trailcurrentoss/TrailCurrentWaveshareEsp32s3Remote/src/ui/screens.c

#include <string.h>

#include "screens.h"
#include "images.h"
#include "fonts.h"
#include "actions.h"
#include "vars.h"
#include "styles.h"
#include "ui.h"

#include <string.h>

objects_t objects;
lv_obj_t *tick_value_change_obj;
uint32_t active_theme_index = 0;

void create_screen_home() {
    lv_obj_t *obj = lv_obj_create(0);
    objects.home = obj;
    lv_obj_set_pos(obj, 0, 0);
    lv_obj_set_size(obj, 800, 480);
    add_style_style_screen_default(obj);
    {
        lv_obj_t *parent_obj = obj;
        {
            // HomePageBottomNavBar
            lv_obj_t *obj = lv_obj_create(parent_obj);
            objects.home_page_bottom_nav_bar = obj;
            lv_obj_set_pos(obj, 0, 0);
            lv_obj_set_size(obj, 800, 60);
            lv_obj_set_style_pad_left(obj, 0, LV_PART_MAIN | LV_STATE_DEFAULT);
            lv_obj_set_style_pad_top(obj, 0, LV_PART_MAIN | LV_STATE_DEFAULT);
            lv_obj_set_style_pad_right(obj, 0, LV_PART_MAIN | LV_STATE_DEFAULT);
            lv_obj_set_style_pad_bottom(obj, 0, LV_PART_MAIN | LV_STATE_DEFAULT);
            lv_obj_set_style_bg_opa(obj, 0, LV_PART_MAIN | LV_STATE_DEFAULT);
            lv_obj_set_style_border_width(obj, 0, LV_PART_MAIN | LV_STATE_DEFAULT);
            create_user_widget_bottom_nav_bar(obj, 10);
            lv_obj_set_style_align(obj, LV_ALIGN_BOTTOM_LEFT, LV_PART_MAIN | LV_STATE_DEFAULT);
        }
        {
            lv_obj_t *obj = lv_obj_create(parent_obj);
            lv_obj_set_pos(obj, -310, 30);
            lv_obj_set_size(obj, 150, 150);
            lv_obj_clear_flag(obj, LV_OBJ_FLAG_CLICKABLE|LV_OBJ_FLAG_CLICK_FOCUSABLE|LV_OBJ_FLAG_GESTURE_BUBBLE|LV_OBJ_FLAG_PRESS_LOCK|LV_OBJ_FLAG_SCROLLABLE|LV_OBJ_FLAG_SCROLL_CHAIN_HOR|LV_OBJ_FLAG_SCROLL_CHAIN_VER|LV_OBJ_FLAG_SCROLL_ELASTIC|LV_OBJ_FLAG_SCROLL_MOMENTUM|LV_OBJ_FLAG_SCROLL_WITH_ARROW|LV_OBJ_FLAG_SNAPPABLE);
            add_style_panel_nav_bar(obj);
            lv_obj_set_style_align(obj, LV_ALIGN_TOP_MID, LV_PART_MAIN | LV_STATE_DEFAULT);
            {
                lv_obj_t *parent_obj = obj;
                {
                    // LabelWarningIconTrailerConnected
                    lv_obj_t *obj = lv_label_create(parent_obj);
                    objects.label_warning_icon_trailer_connected = obj;
                    lv_obj_set_pos(obj, 0, 20);
                    lv_obj_set_size(obj, LV_SIZE_CONTENT, LV_SIZE_CONTENT);
                    add_style_label_fa32_icon(obj);
                    lv_obj_set_style_text_color(obj, lv_color_hex(theme_colors[active_theme_index][0]), LV_PART_MAIN | LV_STATE_DEFAULT);
                    lv_obj_set_style_align(obj, LV_ALIGN_TOP_MID, LV_PART_MAIN | LV_STATE_DEFAULT);
                    lv_obj_set_style_text_color(obj, lv_color_hex(theme_colors[active_theme_index][8]), LV_PART_MAIN | LV_STATE_CHECKED);
                    lv_label_set_text(obj, "\uf8ff");
                }
                {
                    // LabelWarningTextTrailerConnected
                    lv_obj_t *obj = lv_label_create(parent_obj);
                    objects.label_warning_text_trailer_connected = obj;
                    lv_obj_set_pos(obj, 0, 0);
                    lv_obj_set_size(obj, LV_SIZE_CONTENT, LV_SIZE_CONTENT);
                    add_style_label_default(obj);
                    lv_obj_set_style_text_color(obj, lv_color_hex(theme_colors[active_theme_index][0]), LV_PART_MAIN | LV_STATE_DEFAULT);
                    lv_obj_set_style_align(obj, LV_ALIGN_BOTTOM_MID, LV_PART_MAIN | LV_STATE_DEFAULT);
                    lv_obj_set_style_text_align(obj, LV_TEXT_ALIGN_CENTER, LV_PART_MAIN | LV_STATE_DEFAULT);
                    lv_obj_set_style_text_font(obj, &lv_font_montserrat_24, LV_PART_MAIN | LV_STATE_DEFAULT);
                    lv_obj_set_style_text_color(obj, lv_color_hex(theme_colors[active_theme_index][8]), LV_PART_MAIN | LV_STATE_CHECKED);
                    lv_obj_set_style_align(obj, LV_ALIGN_BOTTOM_MID, LV_PART_MAIN | LV_STATE_CHECKED);
                    lv_obj_set_style_text_font(obj, &lv_font_montserrat_24, LV_PART_MAIN | LV_STATE_CHECKED);
                    lv_label_set_text(obj, "Connected");
                }
            }
        }
        {
            lv_obj_t *obj = lv_obj_create(parent_obj);
            lv_obj_set_pos(obj, -155, 30);
            lv_obj_set_size(obj, 150, 150);
            lv_obj_clear_flag(obj, LV_OBJ_FLAG_CLICKABLE|LV_OBJ_FLAG_CLICK_FOCUSABLE|LV_OBJ_FLAG_GESTURE_BUBBLE|LV_OBJ_FLAG_PRESS_LOCK|LV_OBJ_FLAG_SCROLLABLE|LV_OBJ_FLAG_SCROLL_CHAIN_HOR|LV_OBJ_FLAG_SCROLL_CHAIN_VER|LV_OBJ_FLAG_SCROLL_ELASTIC|LV_OBJ_FLAG_SCROLL_MOMENTUM|LV_OBJ_FLAG_SCROLL_WITH_ARROW|LV_OBJ_FLAG_SNAPPABLE);
            add_style_panel_nav_bar(obj);
            lv_obj_set_style_align(obj, LV_ALIGN_TOP_MID, LV_PART_MAIN | LV_STATE_DEFAULT);
            {
                lv_obj_t *parent_obj = obj;
                {
                    // LabelWarningIconFridge
                    lv_obj_t *obj = lv_label_create(parent_obj);
                    objects.label_warning_icon_fridge = obj;
                    lv_obj_set_pos(obj, 0, 20);
                    lv_obj_set_size(obj, LV_SIZE_CONTENT, LV_SIZE_CONTENT);
                    add_style_label_fa32_icon(obj);
                    lv_obj_set_style_text_color(obj, lv_color_hex(theme_colors[active_theme_index][0]), LV_PART_MAIN | LV_STATE_DEFAULT);
                    lv_obj_set_style_align(obj, LV_ALIGN_TOP_MID, LV_PART_MAIN | LV_STATE_DEFAULT);
                    lv_obj_set_style_text_color(obj, lv_color_hex(theme_colors[active_theme_index][8]), LV_PART_MAIN | LV_STATE_CHECKED);
                    lv_label_set_text(obj, "\uf2dc");
                }
                {
                    // LabelWarningTextFridge
                    lv_obj_t *obj = lv_label_create(parent_obj);
                    objects.label_warning_text_fridge = obj;
                    lv_obj_set_pos(obj, 0, 0);
                    lv_obj_set_size(obj, LV_SIZE_CONTENT, LV_SIZE_CONTENT);
                    add_style_label_default(obj);
                    lv_obj_set_style_text_color(obj, lv_color_hex(theme_colors[active_theme_index][0]), LV_PART_MAIN | LV_STATE_DEFAULT);
                    lv_obj_set_style_align(obj, LV_ALIGN_BOTTOM_MID, LV_PART_MAIN | LV_STATE_DEFAULT);
                    lv_obj_set_style_text_align(obj, LV_TEXT_ALIGN_CENTER, LV_PART_MAIN | LV_STATE_DEFAULT);
                    lv_obj_set_style_text_font(obj, &lv_font_montserrat_24, LV_PART_MAIN | LV_STATE_DEFAULT);
                    lv_obj_set_style_text_color(obj, lv_color_hex(theme_colors[active_theme_index][8]), LV_PART_MAIN | LV_STATE_CHECKED);
                    lv_obj_set_style_align(obj, LV_ALIGN_BOTTOM_MID, LV_PART_MAIN | LV_STATE_CHECKED);
                    lv_obj_set_style_text_font(obj, &lv_font_montserrat_24, LV_PART_MAIN | LV_STATE_CHECKED);
                    lv_label_set_text(obj, "Fridge");
                }
            }
        }
        {
            lv_obj_t *obj = lv_obj_create(parent_obj);
            lv_obj_set_pos(obj, 0, 30);
            lv_obj_set_size(obj, 150, 150);
            lv_obj_clear_flag(obj, LV_OBJ_FLAG_CLICKABLE|LV_OBJ_FLAG_CLICK_FOCUSABLE|LV_OBJ_FLAG_GESTURE_BUBBLE|LV_OBJ_FLAG_PRESS_LOCK|LV_OBJ_FLAG_SCROLLABLE|LV_OBJ_FLAG_SCROLL_CHAIN_HOR|LV_OBJ_FLAG_SCROLL_CHAIN_VER|LV_OBJ_FLAG_SCROLL_ELASTIC|LV_OBJ_FLAG_SCROLL_MOMENTUM|LV_OBJ_FLAG_SCROLL_WITH_ARROW|LV_OBJ_FLAG_SNAPPABLE);
            add_style_panel_nav_bar(obj);
            lv_obj_set_style_align(obj, LV_ALIGN_TOP_MID, LV_PART_MAIN | LV_STATE_DEFAULT);
            {
                lv_obj_t *parent_obj = obj;
                {
                    // LabelWarningIconRearDoor
                    lv_obj_t *obj = lv_label_create(parent_obj);
                    objects.label_warning_icon_rear_door = obj;
                    lv_obj_set_pos(obj, 0, 20);
                    lv_obj_set_size(obj, LV_SIZE_CONTENT, LV_SIZE_CONTENT);
                    add_style_label_fa32_icon(obj);
                    lv_obj_set_style_text_color(obj, lv_color_hex(theme_colors[active_theme_index][0]), LV_PART_MAIN | LV_STATE_DEFAULT);
                    lv_obj_set_style_align(obj, LV_ALIGN_TOP_MID, LV_PART_MAIN | LV_STATE_DEFAULT);
                    lv_obj_set_style_text_color(obj, lv_color_hex(theme_colors[active_theme_index][8]), LV_PART_MAIN | LV_STATE_CHECKED);
                    lv_label_set_text(obj, "\uf494");
                }
                {
                    // LabelWarningTextRearDoor
                    lv_obj_t *obj = lv_label_create(parent_obj);
                    objects.label_warning_text_rear_door = obj;
                    lv_obj_set_pos(obj, 0, 0);
                    lv_obj_set_size(obj, LV_SIZE_CONTENT, LV_SIZE_CONTENT);
                    add_style_label_default(obj);
                    lv_obj_set_style_text_color(obj, lv_color_hex(theme_colors[active_theme_index][0]), LV_PART_MAIN | LV_STATE_DEFAULT);
                    lv_obj_set_style_align(obj, LV_ALIGN_BOTTOM_MID, LV_PART_MAIN | LV_STATE_DEFAULT);
                    lv_obj_set_style_text_align(obj, LV_TEXT_ALIGN_CENTER, LV_PART_MAIN | LV_STATE_DEFAULT);
                    lv_obj_set_style_text_font(obj, &lv_font_montserrat_24, LV_PART_MAIN | LV_STATE_DEFAULT);
                    lv_obj_set_style_text_color(obj, lv_color_hex(theme_colors[active_theme_index][8]), LV_PART_MAIN | LV_STATE_CHECKED);
                    lv_obj_set_style_align(obj, LV_ALIGN_BOTTOM_MID, LV_PART_MAIN | LV_STATE_CHECKED);
                    lv_obj_set_style_text_font(obj, &lv_font_montserrat_24, LV_PART_MAIN | LV_STATE_CHECKED);
                    lv_label_set_text(obj, "Rear Door");
                }
            }
        }
        {
            lv_obj_t *obj = lv_obj_create(parent_obj);
            lv_obj_set_pos(obj, 155, 30);
            lv_obj_set_size(obj, 150, 150);
            lv_obj_clear_flag(obj, LV_OBJ_FLAG_CLICKABLE|LV_OBJ_FLAG_CLICK_FOCUSABLE|LV_OBJ_FLAG_GESTURE_BUBBLE|LV_OBJ_FLAG_PRESS_LOCK|LV_OBJ_FLAG_SCROLLABLE|LV_OBJ_FLAG_SCROLL_CHAIN_HOR|LV_OBJ_FLAG_SCROLL_CHAIN_VER|LV_OBJ_FLAG_SCROLL_ELASTIC|LV_OBJ_FLAG_SCROLL_MOMENTUM|LV_OBJ_FLAG_SCROLL_WITH_ARROW|LV_OBJ_FLAG_SNAPPABLE);
            add_style_panel_nav_bar(obj);
            lv_obj_set_style_align(obj, LV_ALIGN_TOP_MID, LV_PART_MAIN | LV_STATE_DEFAULT);
            {
                lv_obj_t *parent_obj = obj;
                {
                    // LabelWarningIconCabinets
                    lv_obj_t *obj = lv_label_create(parent_obj);
                    objects.label_warning_icon_cabinets = obj;
                    lv_obj_set_pos(obj, 0, 20);
                    lv_obj_set_size(obj, LV_SIZE_CONTENT, LV_SIZE_CONTENT);
                    add_style_label_fa32_icon(obj);
                    lv_obj_set_style_text_color(obj, lv_color_hex(theme_colors[active_theme_index][0]), LV_PART_MAIN | LV_STATE_DEFAULT);
                    lv_obj_set_style_align(obj, LV_ALIGN_TOP_MID, LV_PART_MAIN | LV_STATE_DEFAULT);
                    lv_obj_set_style_text_color(obj, lv_color_hex(theme_colors[active_theme_index][8]), LV_PART_MAIN | LV_STATE_CHECKED);
                    lv_label_set_text(obj, "\uf466");
                }
                {
                    // LabelWarningTextCabinets
                    lv_obj_t *obj = lv_label_create(parent_obj);
                    objects.label_warning_text_cabinets = obj;
                    lv_obj_set_pos(obj, 0, 0);
                    lv_obj_set_size(obj, LV_SIZE_CONTENT, LV_SIZE_CONTENT);
                    add_style_label_default(obj);
                    lv_obj_set_style_text_color(obj, lv_color_hex(theme_colors[active_theme_index][0]), LV_PART_MAIN | LV_STATE_DEFAULT);
                    lv_obj_set_style_align(obj, LV_ALIGN_BOTTOM_MID, LV_PART_MAIN | LV_STATE_DEFAULT);
                    lv_obj_set_style_text_align(obj, LV_TEXT_ALIGN_CENTER, LV_PART_MAIN | LV_STATE_DEFAULT);
                    lv_obj_set_style_text_font(obj, &lv_font_montserrat_24, LV_PART_MAIN | LV_STATE_DEFAULT);
                    lv_obj_set_style_text_color(obj, lv_color_hex(theme_colors[active_theme_index][8]), LV_PART_MAIN | LV_STATE_CHECKED);
                    lv_obj_set_style_align(obj, LV_ALIGN_BOTTOM_MID, LV_PART_MAIN | LV_STATE_CHECKED);
                    lv_obj_set_style_text_font(obj, &lv_font_montserrat_24, LV_PART_MAIN | LV_STATE_CHECKED);
                    lv_label_set_text(obj, "Cabinets");
                }
            }
        }
        {
            lv_obj_t *obj = lv_obj_create(parent_obj);
            lv_obj_set_pos(obj, 310, 30);
            lv_obj_set_size(obj, 150, 150);
            lv_obj_clear_flag(obj, LV_OBJ_FLAG_CLICKABLE|LV_OBJ_FLAG_CLICK_FOCUSABLE|LV_OBJ_FLAG_GESTURE_BUBBLE|LV_OBJ_FLAG_PRESS_LOCK|LV_OBJ_FLAG_SCROLLABLE|LV_OBJ_FLAG_SCROLL_CHAIN_HOR|LV_OBJ_FLAG_SCROLL_CHAIN_VER|LV_OBJ_FLAG_SCROLL_ELASTIC|LV_OBJ_FLAG_SCROLL_MOMENTUM|LV_OBJ_FLAG_SCROLL_WITH_ARROW|LV_OBJ_FLAG_SNAPPABLE);
            add_style_panel_nav_bar(obj);
            lv_obj_set_style_align(obj, LV_ALIGN_TOP_MID, LV_PART_MAIN | LV_STATE_DEFAULT);
            {
                lv_obj_t *parent_obj = obj;
                {
                    // LabelWarningIconSideDoor
                    lv_obj_t *obj = lv_label_create(parent_obj);
                    objects.label_warning_icon_side_door = obj;
                    lv_obj_set_pos(obj, 0, 20);
                    lv_obj_set_size(obj, LV_SIZE_CONTENT, LV_SIZE_CONTENT);
                    add_style_label_fa32_icon(obj);
                    lv_obj_set_style_text_color(obj, lv_color_hex(theme_colors[active_theme_index][0]), LV_PART_MAIN | LV_STATE_DEFAULT);
                    lv_obj_set_style_align(obj, LV_ALIGN_TOP_MID, LV_PART_MAIN | LV_STATE_DEFAULT);
                    lv_obj_set_style_text_color(obj, lv_color_hex(theme_colors[active_theme_index][8]), LV_PART_MAIN | LV_STATE_CHECKED);
                    lv_label_set_text(obj, "\uf52a");
                }
                {
                    // LabelWarningTextSideDoor
                    lv_obj_t *obj = lv_label_create(parent_obj);
                    objects.label_warning_text_side_door = obj;
                    lv_obj_set_pos(obj, 0, 0);
                    lv_obj_set_size(obj, LV_SIZE_CONTENT, LV_SIZE_CONTENT);
                    add_style_label_default(obj);
                    lv_obj_set_style_text_color(obj, lv_color_hex(theme_colors[active_theme_index][0]), LV_PART_MAIN | LV_STATE_DEFAULT);
                    lv_obj_set_style_align(obj, LV_ALIGN_BOTTOM_MID, LV_PART_MAIN | LV_STATE_DEFAULT);
                    lv_obj_set_style_text_align(obj, LV_TEXT_ALIGN_CENTER, LV_PART_MAIN | LV_STATE_DEFAULT);
                    lv_obj_set_style_text_font(obj, &lv_font_montserrat_24, LV_PART_MAIN | LV_STATE_DEFAULT);
                    lv_obj_set_style_text_color(obj, lv_color_hex(theme_colors[active_theme_index][8]), LV_PART_MAIN | LV_STATE_CHECKED);
                    lv_obj_set_style_align(obj, LV_ALIGN_BOTTOM_MID, LV_PART_MAIN | LV_STATE_CHECKED);
                    lv_obj_set_style_text_font(obj, &lv_font_montserrat_24, LV_PART_MAIN | LV_STATE_CHECKED);
                    lv_label_set_text(obj, "Side Door");
                }
            }
        }
        {
            lv_obj_t *obj = lv_obj_create(parent_obj);
            lv_obj_set_pos(obj, -310, 200);
            lv_obj_set_size(obj, 150, 150);
            lv_obj_clear_flag(obj, LV_OBJ_FLAG_CLICKABLE|LV_OBJ_FLAG_CLICK_FOCUSABLE|LV_OBJ_FLAG_GESTURE_BUBBLE|LV_OBJ_FLAG_PRESS_LOCK|LV_OBJ_FLAG_SCROLLABLE|LV_OBJ_FLAG_SCROLL_CHAIN_HOR|LV_OBJ_FLAG_SCROLL_CHAIN_VER|LV_OBJ_FLAG_SCROLL_ELASTIC|LV_OBJ_FLAG_SCROLL_MOMENTUM|LV_OBJ_FLAG_SCROLL_WITH_ARROW|LV_OBJ_FLAG_SNAPPABLE);
            add_style_panel_nav_bar(obj);
            lv_obj_set_style_align(obj, LV_ALIGN_TOP_MID, LV_PART_MAIN | LV_STATE_DEFAULT);
            {
                lv_obj_t *parent_obj = obj;
                {
                    // LabelWarningIconLights
                    lv_obj_t *obj = lv_label_create(parent_obj);
                    objects.label_warning_icon_lights = obj;
                    lv_obj_set_pos(obj, 0, 20);
                    lv_obj_set_size(obj, LV_SIZE_CONTENT, LV_SIZE_CONTENT);
                    add_style_label_fa32_icon(obj);
                    lv_obj_set_style_text_color(obj, lv_color_hex(theme_colors[active_theme_index][0]), LV_PART_MAIN | LV_STATE_DEFAULT);
                    lv_obj_set_style_align(obj, LV_ALIGN_TOP_MID, LV_PART_MAIN | LV_STATE_DEFAULT);
                    lv_obj_set_style_text_color(obj, lv_color_hex(theme_colors[active_theme_index][8]), LV_PART_MAIN | LV_STATE_CHECKED);
                    lv_label_set_text(obj, "\uf0eb");
                }
                {
                    // LabelWarningTextLights
                    lv_obj_t *obj = lv_label_create(parent_obj);
                    objects.label_warning_text_lights = obj;
                    lv_obj_set_pos(obj, 0, 0);
                    lv_obj_set_size(obj, LV_SIZE_CONTENT, LV_SIZE_CONTENT);
                    add_style_label_default(obj);
                    lv_obj_set_style_text_color(obj, lv_color_hex(theme_colors[active_theme_index][0]), LV_PART_MAIN | LV_STATE_DEFAULT);
                    lv_obj_set_style_align(obj, LV_ALIGN_BOTTOM_MID, LV_PART_MAIN | LV_STATE_DEFAULT);
                    lv_obj_set_style_text_align(obj, LV_TEXT_ALIGN_CENTER, LV_PART_MAIN | LV_STATE_DEFAULT);
                    lv_obj_set_style_text_font(obj, &lv_font_montserrat_24, LV_PART_MAIN | LV_STATE_DEFAULT);
                    lv_obj_set_style_text_color(obj, lv_color_hex(theme_colors[active_theme_index][8]), LV_PART_MAIN | LV_STATE_CHECKED);
                    lv_obj_set_style_align(obj, LV_ALIGN_BOTTOM_MID, LV_PART_MAIN | LV_STATE_CHECKED);
                    lv_obj_set_style_text_font(obj, &lv_font_montserrat_24, LV_PART_MAIN | LV_STATE_CHECKED);
                    lv_label_set_text(obj, "Lights");
                }
            }
        }
        {
            lv_obj_t *obj = lv_obj_create(parent_obj);
            lv_obj_set_pos(obj, -155, 200);
            lv_obj_set_size(obj, 150, 150);
            lv_obj_clear_flag(obj, LV_OBJ_FLAG_CLICKABLE|LV_OBJ_FLAG_CLICK_FOCUSABLE|LV_OBJ_FLAG_GESTURE_BUBBLE|LV_OBJ_FLAG_PRESS_LOCK|LV_OBJ_FLAG_SCROLLABLE|LV_OBJ_FLAG_SCROLL_CHAIN_HOR|LV_OBJ_FLAG_SCROLL_CHAIN_VER|LV_OBJ_FLAG_SCROLL_ELASTIC|LV_OBJ_FLAG_SCROLL_MOMENTUM|LV_OBJ_FLAG_SCROLL_WITH_ARROW|LV_OBJ_FLAG_SNAPPABLE);
            add_style_panel_nav_bar(obj);
            lv_obj_set_style_align(obj, LV_ALIGN_TOP_MID, LV_PART_MAIN | LV_STATE_DEFAULT);
            {
                lv_obj_t *parent_obj = obj;
                {
                    // LabelWarningIconWater
                    lv_obj_t *obj = lv_label_create(parent_obj);
                    objects.label_warning_icon_water = obj;
                    lv_obj_set_pos(obj, 0, 20);
                    lv_obj_set_size(obj, LV_SIZE_CONTENT, LV_SIZE_CONTENT);
                    add_style_label_fa32_icon(obj);
                    lv_obj_set_style_text_color(obj, lv_color_hex(theme_colors[active_theme_index][0]), LV_PART_MAIN | LV_STATE_DEFAULT);
                    lv_obj_set_style_align(obj, LV_ALIGN_TOP_MID, LV_PART_MAIN | LV_STATE_DEFAULT);
                    lv_obj_set_style_text_color(obj, lv_color_hex(theme_colors[active_theme_index][8]), LV_PART_MAIN | LV_STATE_CHECKED);
                    lv_label_set_text(obj, "\ue005");
                }
                {
                    // LabelWarningTextWater
                    lv_obj_t *obj = lv_label_create(parent_obj);
                    objects.label_warning_text_water = obj;
                    lv_obj_set_pos(obj, 0, 0);
                    lv_obj_set_size(obj, LV_SIZE_CONTENT, LV_SIZE_CONTENT);
                    add_style_label_default(obj);
                    lv_obj_set_style_text_color(obj, lv_color_hex(theme_colors[active_theme_index][0]), LV_PART_MAIN | LV_STATE_DEFAULT);
                    lv_obj_set_style_align(obj, LV_ALIGN_BOTTOM_MID, LV_PART_MAIN | LV_STATE_DEFAULT);
                    lv_obj_set_style_text_align(obj, LV_TEXT_ALIGN_CENTER, LV_PART_MAIN | LV_STATE_DEFAULT);
                    lv_obj_set_style_text_font(obj, &lv_font_montserrat_24, LV_PART_MAIN | LV_STATE_DEFAULT);
                    lv_obj_set_style_text_color(obj, lv_color_hex(theme_colors[active_theme_index][8]), LV_PART_MAIN | LV_STATE_CHECKED);
                    lv_obj_set_style_align(obj, LV_ALIGN_BOTTOM_MID, LV_PART_MAIN | LV_STATE_CHECKED);
                    lv_obj_set_style_text_font(obj, &lv_font_montserrat_24, LV_PART_MAIN | LV_STATE_CHECKED);
                    lv_label_set_text(obj, "Water");
                }
            }
        }
        {
            lv_obj_t *obj = lv_obj_create(parent_obj);
            lv_obj_set_pos(obj, 0, 200);
            lv_obj_set_size(obj, 150, 150);
            lv_obj_clear_flag(obj, LV_OBJ_FLAG_CLICKABLE|LV_OBJ_FLAG_CLICK_FOCUSABLE|LV_OBJ_FLAG_GESTURE_BUBBLE|LV_OBJ_FLAG_PRESS_LOCK|LV_OBJ_FLAG_SCROLLABLE|LV_OBJ_FLAG_SCROLL_CHAIN_HOR|LV_OBJ_FLAG_SCROLL_CHAIN_VER|LV_OBJ_FLAG_SCROLL_ELASTIC|LV_OBJ_FLAG_SCROLL_MOMENTUM|LV_OBJ_FLAG_SCROLL_WITH_ARROW|LV_OBJ_FLAG_SNAPPABLE);
            add_style_panel_nav_bar(obj);
            lv_obj_set_style_align(obj, LV_ALIGN_TOP_MID, LV_PART_MAIN | LV_STATE_DEFAULT);
            {
                lv_obj_t *parent_obj = obj;
                {
                    // LabelWarningIconFan
                    lv_obj_t *obj = lv_label_create(parent_obj);
                    objects.label_warning_icon_fan = obj;
                    lv_obj_set_pos(obj, 0, 20);
                    lv_obj_set_size(obj, LV_SIZE_CONTENT, LV_SIZE_CONTENT);
                    add_style_label_fa32_icon(obj);
                    lv_obj_set_style_text_color(obj, lv_color_hex(theme_colors[active_theme_index][0]), LV_PART_MAIN | LV_STATE_DEFAULT);
                    lv_obj_set_style_align(obj, LV_ALIGN_TOP_MID, LV_PART_MAIN | LV_STATE_DEFAULT);
                    lv_obj_set_style_text_color(obj, lv_color_hex(theme_colors[active_theme_index][8]), LV_PART_MAIN | LV_STATE_CHECKED);
                    lv_label_set_text(obj, "\uf863");
                }
                {
                    // LabelWarningTextFan
                    lv_obj_t *obj = lv_label_create(parent_obj);
                    objects.label_warning_text_fan = obj;
                    lv_obj_set_pos(obj, 0, 0);
                    lv_obj_set_size(obj, LV_SIZE_CONTENT, LV_SIZE_CONTENT);
                    add_style_label_default(obj);
                    lv_obj_set_style_text_color(obj, lv_color_hex(theme_colors[active_theme_index][0]), LV_PART_MAIN | LV_STATE_DEFAULT);
                    lv_obj_set_style_align(obj, LV_ALIGN_BOTTOM_MID, LV_PART_MAIN | LV_STATE_DEFAULT);
                    lv_obj_set_style_text_align(obj, LV_TEXT_ALIGN_CENTER, LV_PART_MAIN | LV_STATE_DEFAULT);
                    lv_obj_set_style_text_font(obj, &lv_font_montserrat_24, LV_PART_MAIN | LV_STATE_DEFAULT);
                    lv_obj_set_style_text_color(obj, lv_color_hex(theme_colors[active_theme_index][8]), LV_PART_MAIN | LV_STATE_CHECKED);
                    lv_obj_set_style_align(obj, LV_ALIGN_BOTTOM_MID, LV_PART_MAIN | LV_STATE_CHECKED);
                    lv_obj_set_style_text_font(obj, &lv_font_montserrat_24, LV_PART_MAIN | LV_STATE_CHECKED);
                    lv_label_set_text(obj, "Fan");
                }
            }
        }
        {
            lv_obj_t *obj = lv_obj_create(parent_obj);
            lv_obj_set_pos(obj, 155, 200);
            lv_obj_set_size(obj, 150, 150);
            lv_obj_clear_flag(obj, LV_OBJ_FLAG_CLICKABLE|LV_OBJ_FLAG_CLICK_FOCUSABLE|LV_OBJ_FLAG_GESTURE_BUBBLE|LV_OBJ_FLAG_PRESS_LOCK|LV_OBJ_FLAG_SCROLLABLE|LV_OBJ_FLAG_SCROLL_CHAIN_HOR|LV_OBJ_FLAG_SCROLL_CHAIN_VER|LV_OBJ_FLAG_SCROLL_ELASTIC|LV_OBJ_FLAG_SCROLL_MOMENTUM|LV_OBJ_FLAG_SCROLL_WITH_ARROW|LV_OBJ_FLAG_SNAPPABLE);
            add_style_panel_nav_bar(obj);
            lv_obj_set_style_align(obj, LV_ALIGN_TOP_MID, LV_PART_MAIN | LV_STATE_DEFAULT);
            {
                lv_obj_t *parent_obj = obj;
                {
                    // LabelWarningIconStabilizers
                    lv_obj_t *obj = lv_label_create(parent_obj);
                    objects.label_warning_icon_stabilizers = obj;
                    lv_obj_set_pos(obj, 0, 20);
                    lv_obj_set_size(obj, LV_SIZE_CONTENT, LV_SIZE_CONTENT);
                    add_style_label_fa32_icon(obj);
                    lv_obj_set_style_text_color(obj, lv_color_hex(theme_colors[active_theme_index][0]), LV_PART_MAIN | LV_STATE_DEFAULT);
                    lv_obj_set_style_align(obj, LV_ALIGN_TOP_MID, LV_PART_MAIN | LV_STATE_DEFAULT);
                    lv_obj_set_style_text_color(obj, lv_color_hex(theme_colors[active_theme_index][8]), LV_PART_MAIN | LV_STATE_CHECKED);
                    lv_label_set_text(obj, "\uf13d");
                }
                {
                    // LabelWarningTextStabilizers
                    lv_obj_t *obj = lv_label_create(parent_obj);
                    objects.label_warning_text_stabilizers = obj;
                    lv_obj_set_pos(obj, 0, 0);
                    lv_obj_set_size(obj, LV_SIZE_CONTENT, LV_SIZE_CONTENT);
                    add_style_label_default(obj);
                    lv_obj_set_style_text_color(obj, lv_color_hex(theme_colors[active_theme_index][0]), LV_PART_MAIN | LV_STATE_DEFAULT);
                    lv_obj_set_style_align(obj, LV_ALIGN_BOTTOM_MID, LV_PART_MAIN | LV_STATE_DEFAULT);
                    lv_obj_set_style_text_align(obj, LV_TEXT_ALIGN_CENTER, LV_PART_MAIN | LV_STATE_DEFAULT);
                    lv_obj_set_style_text_font(obj, &lv_font_montserrat_24, LV_PART_MAIN | LV_STATE_DEFAULT);
                    lv_obj_set_style_text_color(obj, lv_color_hex(theme_colors[active_theme_index][8]), LV_PART_MAIN | LV_STATE_CHECKED);
                    lv_obj_set_style_align(obj, LV_ALIGN_BOTTOM_MID, LV_PART_MAIN | LV_STATE_CHECKED);
                    lv_obj_set_style_text_font(obj, &lv_font_montserrat_24, LV_PART_MAIN | LV_STATE_CHECKED);
                    lv_label_set_text(obj, "Stabilizers");
                }
            }
        }
        {
            lv_obj_t *obj = lv_obj_create(parent_obj);
            lv_obj_set_pos(obj, 310, 200);
            lv_obj_set_size(obj, 150, 150);
            lv_obj_clear_flag(obj, LV_OBJ_FLAG_CLICKABLE|LV_OBJ_FLAG_CLICK_FOCUSABLE|LV_OBJ_FLAG_GESTURE_BUBBLE|LV_OBJ_FLAG_PRESS_LOCK|LV_OBJ_FLAG_SCROLLABLE|LV_OBJ_FLAG_SCROLL_CHAIN_HOR|LV_OBJ_FLAG_SCROLL_CHAIN_VER|LV_OBJ_FLAG_SCROLL_ELASTIC|LV_OBJ_FLAG_SCROLL_MOMENTUM|LV_OBJ_FLAG_SCROLL_WITH_ARROW|LV_OBJ_FLAG_SNAPPABLE);
            add_style_panel_nav_bar(obj);
            lv_obj_set_style_align(obj, LV_ALIGN_TOP_MID, LV_PART_MAIN | LV_STATE_DEFAULT);
            {
                lv_obj_t *parent_obj = obj;
                {
                    // LabelWarningIconPower
                    lv_obj_t *obj = lv_label_create(parent_obj);
                    objects.label_warning_icon_power = obj;
                    lv_obj_set_pos(obj, 0, 20);
                    lv_obj_set_size(obj, LV_SIZE_CONTENT, LV_SIZE_CONTENT);
                    add_style_label_fa32_icon(obj);
                    lv_obj_set_style_text_color(obj, lv_color_hex(theme_colors[active_theme_index][0]), LV_PART_MAIN | LV_STATE_DEFAULT);
                    lv_obj_set_style_align(obj, LV_ALIGN_TOP_MID, LV_PART_MAIN | LV_STATE_DEFAULT);
                    lv_obj_set_style_text_color(obj, lv_color_hex(theme_colors[active_theme_index][8]), LV_PART_MAIN | LV_STATE_CHECKED);
                    lv_label_set_text(obj, "\uf1e6");
                }
                {
                    // LabelWarningTextPower
                    lv_obj_t *obj = lv_label_create(parent_obj);
                    objects.label_warning_text_power = obj;
                    lv_obj_set_pos(obj, 0, 0);
                    lv_obj_set_size(obj, LV_SIZE_CONTENT, LV_SIZE_CONTENT);
                    add_style_label_default(obj);
                    lv_obj_set_style_text_color(obj, lv_color_hex(theme_colors[active_theme_index][0]), LV_PART_MAIN | LV_STATE_DEFAULT);
                    lv_obj_set_style_align(obj, LV_ALIGN_BOTTOM_MID, LV_PART_MAIN | LV_STATE_DEFAULT);
                    lv_obj_set_style_text_align(obj, LV_TEXT_ALIGN_CENTER, LV_PART_MAIN | LV_STATE_DEFAULT);
                    lv_obj_set_style_text_font(obj, &lv_font_montserrat_24, LV_PART_MAIN | LV_STATE_DEFAULT);
                    lv_obj_set_style_text_color(obj, lv_color_hex(theme_colors[active_theme_index][8]), LV_PART_MAIN | LV_STATE_CHECKED);
                    lv_obj_set_style_align(obj, LV_ALIGN_BOTTOM_MID, LV_PART_MAIN | LV_STATE_CHECKED);
                    lv_obj_set_style_text_font(obj, &lv_font_montserrat_24, LV_PART_MAIN | LV_STATE_CHECKED);
                    lv_label_set_text(obj, "Power");
                }
            }
        }
    }
    
    tick_screen_home();
}

void tick_screen_home() {
    tick_user_widget_bottom_nav_bar(10);
}

void create_screen_trailer() {
    lv_obj_t *obj = lv_obj_create(0);
    objects.trailer = obj;
    lv_obj_set_pos(obj, 0, 0);
    lv_obj_set_size(obj, 800, 480);
    add_style_style_screen_default(obj);
    {
        lv_obj_t *parent_obj = obj;
        {
            // TrailerPageBottomNavBar
            lv_obj_t *obj = lv_obj_create(parent_obj);
            objects.trailer_page_bottom_nav_bar = obj;
            lv_obj_set_pos(obj, 0, 0);
            lv_obj_set_size(obj, 800, 60);
            lv_obj_set_style_pad_left(obj, 0, LV_PART_MAIN | LV_STATE_DEFAULT);
            lv_obj_set_style_pad_top(obj, 0, LV_PART_MAIN | LV_STATE_DEFAULT);
            lv_obj_set_style_pad_right(obj, 0, LV_PART_MAIN | LV_STATE_DEFAULT);
            lv_obj_set_style_pad_bottom(obj, 0, LV_PART_MAIN | LV_STATE_DEFAULT);
            lv_obj_set_style_bg_opa(obj, 0, LV_PART_MAIN | LV_STATE_DEFAULT);
            lv_obj_set_style_border_width(obj, 0, LV_PART_MAIN | LV_STATE_DEFAULT);
            create_user_widget_bottom_nav_bar(obj, 37);
            lv_obj_set_style_align(obj, LV_ALIGN_BOTTOM_LEFT, LV_PART_MAIN | LV_STATE_DEFAULT);
        }
        {
            lv_obj_t *obj = lv_obj_create(parent_obj);
            lv_obj_set_pos(obj, 12, 14);
            lv_obj_set_size(obj, 470, 390);
            lv_obj_clear_flag(obj, LV_OBJ_FLAG_CLICKABLE|LV_OBJ_FLAG_CLICK_FOCUSABLE|LV_OBJ_FLAG_GESTURE_BUBBLE|LV_OBJ_FLAG_PRESS_LOCK|LV_OBJ_FLAG_SCROLLABLE|LV_OBJ_FLAG_SCROLL_CHAIN_HOR|LV_OBJ_FLAG_SCROLL_CHAIN_VER|LV_OBJ_FLAG_SCROLL_ELASTIC|LV_OBJ_FLAG_SCROLL_MOMENTUM|LV_OBJ_FLAG_SCROLL_WITH_ARROW|LV_OBJ_FLAG_SNAPPABLE);
            add_style_style_panel_default(obj);
            {
                lv_obj_t *parent_obj = obj;
                {
                    lv_obj_t *obj = lv_img_create(parent_obj);
                    lv_obj_set_pos(obj, -12, -24);
                    lv_obj_set_size(obj, LV_SIZE_CONTENT, LV_SIZE_CONTENT);
                    lv_img_set_src(obj, &img_trailer_side);
                    lv_obj_set_style_align(obj, LV_ALIGN_CENTER, LV_PART_MAIN | LV_STATE_DEFAULT);
                }
            }
        }
        {
            lv_obj_t *obj = lv_obj_create(parent_obj);
            lv_obj_set_pos(obj, -8, 14);
            lv_obj_set_size(obj, 300, 390);
            lv_obj_clear_flag(obj, LV_OBJ_FLAG_CLICKABLE|LV_OBJ_FLAG_CLICK_FOCUSABLE|LV_OBJ_FLAG_GESTURE_BUBBLE|LV_OBJ_FLAG_PRESS_LOCK|LV_OBJ_FLAG_SCROLLABLE|LV_OBJ_FLAG_SCROLL_CHAIN_HOR|LV_OBJ_FLAG_SCROLL_CHAIN_VER|LV_OBJ_FLAG_SCROLL_ELASTIC|LV_OBJ_FLAG_SCROLL_MOMENTUM|LV_OBJ_FLAG_SCROLL_WITH_ARROW|LV_OBJ_FLAG_SNAPPABLE);
            add_style_style_panel_default(obj);
            lv_obj_set_style_align(obj, LV_ALIGN_TOP_RIGHT, LV_PART_MAIN | LV_STATE_DEFAULT);
            {
                lv_obj_t *parent_obj = obj;
                {
                    lv_obj_t *obj = lv_img_create(parent_obj);
                    lv_obj_set_pos(obj, 0, -10);
                    lv_obj_set_size(obj, LV_SIZE_CONTENT, LV_SIZE_CONTENT);
                    lv_img_set_src(obj, &img_trailer_back);
                    lv_obj_set_style_align(obj, LV_ALIGN_CENTER, LV_PART_MAIN | LV_STATE_DEFAULT);
                }
            }
        }
        {
            // LabelCurrentSpeedValue
            lv_obj_t *obj = lv_label_create(parent_obj);
            objects.label_current_speed_value = obj;
            lv_obj_set_pos(obj, 540, 21);
            lv_obj_set_size(obj, 163, LV_SIZE_CONTENT);
            add_style_label_secondary(obj);
            lv_obj_set_style_text_font(obj, &lv_font_montserrat_36, LV_PART_MAIN | LV_STATE_DEFAULT);
            lv_obj_set_style_text_align(obj, LV_TEXT_ALIGN_RIGHT, LV_PART_MAIN | LV_STATE_DEFAULT);
            lv_label_set_text(obj, "0");
        }
        {
            lv_obj_t *obj = lv_label_create(parent_obj);
            lv_obj_set_pos(obj, 712, 33);
            lv_obj_set_size(obj, LV_SIZE_CONTENT, LV_SIZE_CONTENT);
            add_style_label_default(obj);
            lv_label_set_text(obj, "mph");
        }
        {
            lv_obj_t *obj = lv_label_create(parent_obj);
            lv_obj_set_pos(obj, -348, 34);
            lv_obj_set_size(obj, LV_SIZE_CONTENT, LV_SIZE_CONTENT);
            add_style_label_fa32_icon(obj);
            lv_label_set_text(obj, "\uf7c0");
        }
        {
            // LabelNumberOfSatelliteValue
            lv_obj_t *obj = lv_label_create(parent_obj);
            objects.label_number_of_satellite_value = obj;
            lv_obj_set_pos(obj, 85, 29);
            lv_obj_set_size(obj, 73, LV_SIZE_CONTENT);
            add_style_label_secondary(obj);
            lv_obj_set_style_text_font(obj, &lv_font_montserrat_36, LV_PART_MAIN | LV_STATE_DEFAULT);
            lv_obj_set_style_text_align(obj, LV_TEXT_ALIGN_CENTER, LV_PART_MAIN | LV_STATE_DEFAULT);
            lv_label_set_text(obj, "0");
        }
        {
            // GnssModeValue
            lv_obj_t *obj = lv_label_create(parent_obj);
            objects.gnss_mode_value = obj;
            lv_obj_set_pos(obj, 25, 312);
            lv_obj_set_size(obj, 400, LV_SIZE_CONTENT);
            add_style_label_default(obj);
            lv_obj_set_style_text_align(obj, LV_TEXT_ALIGN_LEFT, LV_PART_MAIN | LV_STATE_DEFAULT);
            lv_label_set_text(obj, "NO SIGNAL");
        }
        {
            lv_obj_t *obj = lv_label_create(parent_obj);
            lv_obj_set_pos(obj, -169, 34);
            lv_obj_set_size(obj, LV_SIZE_CONTENT, LV_SIZE_CONTENT);
            add_style_label_fa32_icon(obj);
            lv_label_set_text(obj, "\uf6fc");
        }
        {
            // LabelAltitudeInFeetValue
            lv_obj_t *obj = lv_label_create(parent_obj);
            objects.label_altitude_in_feet_value = obj;
            lv_obj_set_pos(obj, 262, 29);
            lv_obj_set_size(obj, 163, LV_SIZE_CONTENT);
            add_style_label_secondary(obj);
            lv_obj_set_style_text_font(obj, &lv_font_montserrat_36, LV_PART_MAIN | LV_STATE_DEFAULT);
            lv_obj_set_style_text_align(obj, LV_TEXT_ALIGN_LEFT, LV_PART_MAIN | LV_STATE_DEFAULT);
            lv_label_set_text(obj, "0");
        }
        {
            // LabelCurrentLatValue
            lv_obj_t *obj = lv_label_create(parent_obj);
            objects.label_current_lat_value = obj;
            lv_obj_set_pos(obj, 25, 350);
            lv_obj_set_size(obj, LV_SIZE_CONTENT, LV_SIZE_CONTENT);
            add_style_label_default(obj);
            lv_label_set_text(obj, "0.000000");
        }
        {
            // LabelCurrentLongValue
            lv_obj_t *obj = lv_label_create(parent_obj);
            objects.label_current_long_value = obj;
            lv_obj_set_pos(obj, 173, 350);
            lv_obj_set_size(obj, LV_SIZE_CONTENT, LV_SIZE_CONTENT);
            add_style_label_default(obj);
            lv_label_set_text(obj, "0.000000");
        }
        {
            lv_obj_t *obj = lv_label_create(parent_obj);
            lv_obj_set_pos(obj, 156, 350);
            lv_obj_set_size(obj, LV_SIZE_CONTENT, LV_SIZE_CONTENT);
            add_style_label_default(obj);
            lv_label_set_text(obj, ",");
        }
        {
            lv_obj_t *obj = lv_label_create(parent_obj);
            objects.obj0 = obj;
            lv_obj_set_pos(obj, 552, 312);
            lv_obj_set_size(obj, LV_SIZE_CONTENT, LV_SIZE_CONTENT);
            add_style_label_default(obj);
            lv_obj_set_style_text_align(obj, LV_TEXT_ALIGN_CENTER, LV_PART_MAIN | LV_STATE_DEFAULT);
            lv_obj_set_style_text_color(obj, lv_color_hex(theme_colors[active_theme_index][10]), LV_PART_MAIN | LV_STATE_DEFAULT);
            lv_label_set_text(obj, "32");
        }
        {
            lv_obj_t *obj = lv_label_create(parent_obj);
            objects.obj1 = obj;
            lv_obj_set_pos(obj, 703, 312);
            lv_obj_set_size(obj, LV_SIZE_CONTENT, LV_SIZE_CONTENT);
            add_style_label_default(obj);
            lv_obj_set_style_text_align(obj, LV_TEXT_ALIGN_CENTER, LV_PART_MAIN | LV_STATE_DEFAULT);
            lv_obj_set_style_text_color(obj, lv_color_hex(theme_colors[active_theme_index][10]), LV_PART_MAIN | LV_STATE_DEFAULT);
            lv_label_set_text(obj, "32");
        }
        {
            lv_obj_t *obj = lv_label_create(parent_obj);
            lv_obj_set_pos(obj, 701, 341);
            lv_obj_set_size(obj, LV_SIZE_CONTENT, LV_SIZE_CONTENT);
            add_style_label_default(obj);
            lv_obj_set_style_text_align(obj, LV_TEXT_ALIGN_CENTER, LV_PART_MAIN | LV_STATE_DEFAULT);
            lv_obj_set_style_text_font(obj, &lv_font_montserrat_22, LV_PART_MAIN | LV_STATE_DEFAULT);
            lv_label_set_text(obj, "psi");
        }
        {
            lv_obj_t *obj = lv_label_create(parent_obj);
            lv_obj_set_pos(obj, 552, 339);
            lv_obj_set_size(obj, LV_SIZE_CONTENT, LV_SIZE_CONTENT);
            add_style_label_default(obj);
            lv_obj_set_style_text_align(obj, LV_TEXT_ALIGN_CENTER, LV_PART_MAIN | LV_STATE_DEFAULT);
            lv_obj_set_style_text_font(obj, &lv_font_montserrat_22, LV_PART_MAIN | LV_STATE_DEFAULT);
            lv_label_set_text(obj, "psi");
        }
    }
    
    tick_screen_trailer();
}

void tick_screen_trailer() {
    tick_user_widget_bottom_nav_bar(37);
}

void create_screen_power() {
    lv_obj_t *obj = lv_obj_create(0);
    objects.power = obj;
    lv_obj_set_pos(obj, 0, 0);
    lv_obj_set_size(obj, 800, 480);
    add_style_style_screen_default(obj);
    {
        lv_obj_t *parent_obj = obj;
        {
            // PowerPageBottomNavBar
            lv_obj_t *obj = lv_obj_create(parent_obj);
            objects.power_page_bottom_nav_bar = obj;
            lv_obj_set_pos(obj, 0, 0);
            lv_obj_set_size(obj, 800, 60);
            lv_obj_set_style_pad_left(obj, 0, LV_PART_MAIN | LV_STATE_DEFAULT);
            lv_obj_set_style_pad_top(obj, 0, LV_PART_MAIN | LV_STATE_DEFAULT);
            lv_obj_set_style_pad_right(obj, 0, LV_PART_MAIN | LV_STATE_DEFAULT);
            lv_obj_set_style_pad_bottom(obj, 0, LV_PART_MAIN | LV_STATE_DEFAULT);
            lv_obj_set_style_bg_opa(obj, 0, LV_PART_MAIN | LV_STATE_DEFAULT);
            lv_obj_set_style_border_width(obj, 0, LV_PART_MAIN | LV_STATE_DEFAULT);
            create_user_widget_bottom_nav_bar(obj, 52);
            lv_obj_set_style_align(obj, LV_ALIGN_BOTTOM_LEFT, LV_PART_MAIN | LV_STATE_DEFAULT);
        }
        {
            // PanelControlButtons
            lv_obj_t *obj = lv_obj_create(parent_obj);
            objects.panel_control_buttons = obj;
            lv_obj_set_pos(obj, 380, 9);
            lv_obj_set_size(obj, 400, 400);
            add_style_style_content_panel(obj);
            {
                lv_obj_t *parent_obj = obj;
                {
                    // BtnDevice01
                    lv_obj_t *obj = lv_btn_create(parent_obj);
                    objects.btn_device01 = obj;
                    lv_obj_set_pos(obj, 0, 0);
                    lv_obj_set_size(obj, 120, 120);
                    lv_obj_clear_flag(obj, LV_OBJ_FLAG_GESTURE_BUBBLE|LV_OBJ_FLAG_PRESS_LOCK|LV_OBJ_FLAG_SCROLL_CHAIN_HOR|LV_OBJ_FLAG_SCROLL_CHAIN_VER|LV_OBJ_FLAG_SCROLL_ELASTIC|LV_OBJ_FLAG_SCROLL_MOMENTUM|LV_OBJ_FLAG_SCROLL_ON_FOCUS|LV_OBJ_FLAG_SCROLL_WITH_ARROW|LV_OBJ_FLAG_SNAPPABLE);
                    add_style_style_button_default(obj);
                    {
                        lv_obj_t *parent_obj = obj;
                        {
                            // lblDevice01StatusInd
                            lv_obj_t *obj = lv_label_create(parent_obj);
                            objects.lbl_device01_status_ind = obj;
                            lv_obj_set_pos(obj, 0, 0);
                            lv_obj_set_size(obj, 32, 32);
                            lv_obj_clear_flag(obj, LV_OBJ_FLAG_CLICK_FOCUSABLE|LV_OBJ_FLAG_GESTURE_BUBBLE|LV_OBJ_FLAG_PRESS_LOCK|LV_OBJ_FLAG_SCROLLABLE|LV_OBJ_FLAG_SCROLL_CHAIN_HOR|LV_OBJ_FLAG_SCROLL_CHAIN_VER|LV_OBJ_FLAG_SCROLL_ELASTIC|LV_OBJ_FLAG_SCROLL_MOMENTUM|LV_OBJ_FLAG_SCROLL_WITH_ARROW|LV_OBJ_FLAG_SNAPPABLE);
                            add_style_label_fa32_icon(obj);
                            lv_obj_set_style_text_color(obj, lv_color_hex(theme_colors[active_theme_index][9]), LV_PART_MAIN | LV_STATE_DEFAULT);
                            lv_label_set_text(obj, "\uf7b6");
                        }
                        {
                            // lblDevice01Label
                            lv_obj_t *obj = lv_label_create(parent_obj);
                            objects.lbl_device01_label = obj;
                            lv_obj_set_pos(obj, 0, 0);
                            lv_obj_set_size(obj, LV_SIZE_CONTENT, LV_SIZE_CONTENT);
                            lv_obj_clear_flag(obj, LV_OBJ_FLAG_CLICK_FOCUSABLE|LV_OBJ_FLAG_GESTURE_BUBBLE|LV_OBJ_FLAG_PRESS_LOCK|LV_OBJ_FLAG_SCROLLABLE|LV_OBJ_FLAG_SCROLL_CHAIN_HOR|LV_OBJ_FLAG_SCROLL_CHAIN_VER|LV_OBJ_FLAG_SCROLL_ELASTIC|LV_OBJ_FLAG_SCROLL_MOMENTUM|LV_OBJ_FLAG_SCROLL_WITH_ARROW|LV_OBJ_FLAG_SNAPPABLE);
                            add_style_label_default(obj);
                            lv_obj_set_style_align(obj, LV_ALIGN_BOTTOM_MID, LV_PART_MAIN | LV_STATE_DEFAULT);
                            lv_obj_set_style_text_color(obj, lv_color_hex(theme_colors[active_theme_index][9]), LV_PART_MAIN | LV_STATE_DEFAULT);
                            lv_label_set_text(obj, "Under\nCabinet");
                        }
                    }
                }
                {
                    // BtnDevice02
                    lv_obj_t *obj = lv_btn_create(parent_obj);
                    objects.btn_device02 = obj;
                    lv_obj_set_pos(obj, 0, 0);
                    lv_obj_set_size(obj, 120, 120);
                    add_style_style_button_default(obj);
                    lv_obj_set_style_align(obj, LV_ALIGN_TOP_MID, LV_PART_MAIN | LV_STATE_DEFAULT);
                    {
                        lv_obj_t *parent_obj = obj;
                        {
                            // lblDevice02StatusInd
                            lv_obj_t *obj = lv_label_create(parent_obj);
                            objects.lbl_device02_status_ind = obj;
                            lv_obj_set_pos(obj, 0, 0);
                            lv_obj_set_size(obj, 32, 32);
                            lv_obj_clear_flag(obj, LV_OBJ_FLAG_CLICK_FOCUSABLE|LV_OBJ_FLAG_GESTURE_BUBBLE|LV_OBJ_FLAG_PRESS_LOCK|LV_OBJ_FLAG_SCROLLABLE|LV_OBJ_FLAG_SCROLL_CHAIN_HOR|LV_OBJ_FLAG_SCROLL_CHAIN_VER|LV_OBJ_FLAG_SCROLL_ELASTIC|LV_OBJ_FLAG_SCROLL_MOMENTUM|LV_OBJ_FLAG_SCROLL_WITH_ARROW|LV_OBJ_FLAG_SNAPPABLE);
                            add_style_label_fa32_icon(obj);
                            lv_obj_set_style_text_color(obj, lv_color_hex(theme_colors[active_theme_index][9]), LV_PART_MAIN | LV_STATE_DEFAULT);
                            lv_label_set_text(obj, "\uf2e7");
                        }
                        {
                            // lblDevice02Label
                            lv_obj_t *obj = lv_label_create(parent_obj);
                            objects.lbl_device02_label = obj;
                            lv_obj_set_pos(obj, 0, 0);
                            lv_obj_set_size(obj, LV_SIZE_CONTENT, LV_SIZE_CONTENT);
                            lv_obj_clear_flag(obj, LV_OBJ_FLAG_CLICK_FOCUSABLE|LV_OBJ_FLAG_GESTURE_BUBBLE|LV_OBJ_FLAG_PRESS_LOCK|LV_OBJ_FLAG_SCROLLABLE|LV_OBJ_FLAG_SCROLL_CHAIN_HOR|LV_OBJ_FLAG_SCROLL_CHAIN_VER|LV_OBJ_FLAG_SCROLL_ELASTIC|LV_OBJ_FLAG_SCROLL_MOMENTUM|LV_OBJ_FLAG_SCROLL_WITH_ARROW|LV_OBJ_FLAG_SNAPPABLE);
                            add_style_label_default(obj);
                            lv_obj_set_style_align(obj, LV_ALIGN_BOTTOM_MID, LV_PART_MAIN | LV_STATE_DEFAULT);
                            lv_obj_set_style_text_color(obj, lv_color_hex(theme_colors[active_theme_index][9]), LV_PART_MAIN | LV_STATE_DEFAULT);
                            lv_label_set_text(obj, "Kitchen\nLights");
                        }
                    }
                }
                {
                    // BtnDevice03
                    lv_obj_t *obj = lv_btn_create(parent_obj);
                    objects.btn_device03 = obj;
                    lv_obj_set_pos(obj, 0, 0);
                    lv_obj_set_size(obj, 120, 120);
                    add_style_style_button_default(obj);
                    lv_obj_set_style_align(obj, LV_ALIGN_TOP_RIGHT, LV_PART_MAIN | LV_STATE_DEFAULT);
                    {
                        lv_obj_t *parent_obj = obj;
                        {
                            // lblDevice03StatusInd
                            lv_obj_t *obj = lv_label_create(parent_obj);
                            objects.lbl_device03_status_ind = obj;
                            lv_obj_set_pos(obj, 0, 0);
                            lv_obj_set_size(obj, 32, 32);
                            lv_obj_clear_flag(obj, LV_OBJ_FLAG_CLICK_FOCUSABLE|LV_OBJ_FLAG_GESTURE_BUBBLE|LV_OBJ_FLAG_PRESS_LOCK|LV_OBJ_FLAG_SCROLLABLE|LV_OBJ_FLAG_SCROLL_CHAIN_HOR|LV_OBJ_FLAG_SCROLL_CHAIN_VER|LV_OBJ_FLAG_SCROLL_ELASTIC|LV_OBJ_FLAG_SCROLL_MOMENTUM|LV_OBJ_FLAG_SCROLL_WITH_ARROW|LV_OBJ_FLAG_SNAPPABLE);
                            add_style_label_fa32_icon(obj);
                            lv_obj_set_style_align(obj, LV_ALIGN_TOP_MID, LV_PART_MAIN | LV_STATE_DEFAULT);
                            lv_obj_set_style_text_color(obj, lv_color_hex(theme_colors[active_theme_index][9]), LV_PART_MAIN | LV_STATE_DEFAULT);
                            lv_label_set_text(obj, "\uf52a");
                        }
                        {
                            // lblDevice03Label
                            lv_obj_t *obj = lv_label_create(parent_obj);
                            objects.lbl_device03_label = obj;
                            lv_obj_set_pos(obj, 0, 0);
                            lv_obj_set_size(obj, LV_SIZE_CONTENT, LV_SIZE_CONTENT);
                            lv_obj_clear_flag(obj, LV_OBJ_FLAG_CLICK_FOCUSABLE|LV_OBJ_FLAG_GESTURE_BUBBLE|LV_OBJ_FLAG_PRESS_LOCK|LV_OBJ_FLAG_SCROLLABLE|LV_OBJ_FLAG_SCROLL_CHAIN_HOR|LV_OBJ_FLAG_SCROLL_CHAIN_VER|LV_OBJ_FLAG_SCROLL_ELASTIC|LV_OBJ_FLAG_SCROLL_MOMENTUM|LV_OBJ_FLAG_SCROLL_WITH_ARROW|LV_OBJ_FLAG_SNAPPABLE);
                            add_style_label_default(obj);
                            lv_obj_set_style_align(obj, LV_ALIGN_BOTTOM_MID, LV_PART_MAIN | LV_STATE_DEFAULT);
                            lv_obj_set_style_text_color(obj, lv_color_hex(theme_colors[active_theme_index][9]), LV_PART_MAIN | LV_STATE_DEFAULT);
                            lv_label_set_text(obj, "Entry\nLights");
                        }
                    }
                }
                {
                    // BtnDevice04
                    lv_obj_t *obj = lv_btn_create(parent_obj);
                    objects.btn_device04 = obj;
                    lv_obj_set_pos(obj, 0, 0);
                    lv_obj_set_size(obj, 120, 120);
                    add_style_style_button_default(obj);
                    lv_obj_set_style_align(obj, LV_ALIGN_LEFT_MID, LV_PART_MAIN | LV_STATE_DEFAULT);
                    {
                        lv_obj_t *parent_obj = obj;
                        {
                            // lblDevice04StatusInd
                            lv_obj_t *obj = lv_label_create(parent_obj);
                            objects.lbl_device04_status_ind = obj;
                            lv_obj_set_pos(obj, 0, 0);
                            lv_obj_set_size(obj, 32, 32);
                            lv_obj_clear_flag(obj, LV_OBJ_FLAG_CLICK_FOCUSABLE|LV_OBJ_FLAG_GESTURE_BUBBLE|LV_OBJ_FLAG_PRESS_LOCK|LV_OBJ_FLAG_SCROLLABLE|LV_OBJ_FLAG_SCROLL_CHAIN_HOR|LV_OBJ_FLAG_SCROLL_CHAIN_VER|LV_OBJ_FLAG_SCROLL_ELASTIC|LV_OBJ_FLAG_SCROLL_MOMENTUM|LV_OBJ_FLAG_SCROLL_WITH_ARROW|LV_OBJ_FLAG_SNAPPABLE);
                            add_style_label_fa32_icon(obj);
                            lv_obj_set_style_align(obj, LV_ALIGN_TOP_MID, LV_PART_MAIN | LV_STATE_DEFAULT);
                            lv_obj_set_style_text_color(obj, lv_color_hex(theme_colors[active_theme_index][9]), LV_PART_MAIN | LV_STATE_DEFAULT);
                            lv_label_set_text(obj, "\uf0eb");
                        }
                        {
                            // lblDevice04Label
                            lv_obj_t *obj = lv_label_create(parent_obj);
                            objects.lbl_device04_label = obj;
                            lv_obj_set_pos(obj, 0, 0);
                            lv_obj_set_size(obj, LV_SIZE_CONTENT, LV_SIZE_CONTENT);
                            lv_obj_clear_flag(obj, LV_OBJ_FLAG_CLICK_FOCUSABLE|LV_OBJ_FLAG_GESTURE_BUBBLE|LV_OBJ_FLAG_PRESS_LOCK|LV_OBJ_FLAG_SCROLLABLE|LV_OBJ_FLAG_SCROLL_CHAIN_HOR|LV_OBJ_FLAG_SCROLL_CHAIN_VER|LV_OBJ_FLAG_SCROLL_ELASTIC|LV_OBJ_FLAG_SCROLL_MOMENTUM|LV_OBJ_FLAG_SCROLL_WITH_ARROW|LV_OBJ_FLAG_SNAPPABLE);
                            add_style_label_default(obj);
                            lv_obj_set_style_align(obj, LV_ALIGN_BOTTOM_MID, LV_PART_MAIN | LV_STATE_DEFAULT);
                            lv_obj_set_style_text_color(obj, lv_color_hex(theme_colors[active_theme_index][9]), LV_PART_MAIN | LV_STATE_DEFAULT);
                            lv_label_set_text(obj, "Main\nLights");
                        }
                    }
                }
                {
                    // BtnDevice05
                    lv_obj_t *obj = lv_btn_create(parent_obj);
                    objects.btn_device05 = obj;
                    lv_obj_set_pos(obj, 0, 0);
                    lv_obj_set_size(obj, 120, 120);
                    add_style_style_button_default(obj);
                    lv_obj_set_style_align(obj, LV_ALIGN_CENTER, LV_PART_MAIN | LV_STATE_DEFAULT);
                    {
                        lv_obj_t *parent_obj = obj;
                        {
                            // lblDevice05StatusInd
                            lv_obj_t *obj = lv_label_create(parent_obj);
                            objects.lbl_device05_status_ind = obj;
                            lv_obj_set_pos(obj, 0, 0);
                            lv_obj_set_size(obj, 32, 32);
                            lv_obj_clear_flag(obj, LV_OBJ_FLAG_CLICK_FOCUSABLE|LV_OBJ_FLAG_GESTURE_BUBBLE|LV_OBJ_FLAG_PRESS_LOCK|LV_OBJ_FLAG_SCROLLABLE|LV_OBJ_FLAG_SCROLL_CHAIN_HOR|LV_OBJ_FLAG_SCROLL_CHAIN_VER|LV_OBJ_FLAG_SCROLL_ELASTIC|LV_OBJ_FLAG_SCROLL_MOMENTUM|LV_OBJ_FLAG_SCROLL_WITH_ARROW|LV_OBJ_FLAG_SNAPPABLE);
                            add_style_label_fa32_icon(obj);
                            lv_obj_set_style_align(obj, LV_ALIGN_TOP_MID, LV_PART_MAIN | LV_STATE_DEFAULT);
                            lv_obj_set_style_text_color(obj, lv_color_hex(theme_colors[active_theme_index][9]), LV_PART_MAIN | LV_STATE_DEFAULT);
                            lv_label_set_text(obj, "\uf54f");
                        }
                        {
                            // lblDevice05Label
                            lv_obj_t *obj = lv_label_create(parent_obj);
                            objects.lbl_device05_label = obj;
                            lv_obj_set_pos(obj, 0, 0);
                            lv_obj_set_size(obj, LV_SIZE_CONTENT, LV_SIZE_CONTENT);
                            lv_obj_clear_flag(obj, LV_OBJ_FLAG_CLICK_FOCUSABLE|LV_OBJ_FLAG_GESTURE_BUBBLE|LV_OBJ_FLAG_PRESS_LOCK|LV_OBJ_FLAG_SCROLLABLE|LV_OBJ_FLAG_SCROLL_CHAIN_HOR|LV_OBJ_FLAG_SCROLL_CHAIN_VER|LV_OBJ_FLAG_SCROLL_ELASTIC|LV_OBJ_FLAG_SCROLL_MOMENTUM|LV_OBJ_FLAG_SCROLL_WITH_ARROW|LV_OBJ_FLAG_SNAPPABLE);
                            add_style_label_default(obj);
                            lv_obj_set_style_align(obj, LV_ALIGN_BOTTOM_MID, LV_PART_MAIN | LV_STATE_DEFAULT);
                            lv_obj_set_style_text_color(obj, lv_color_hex(theme_colors[active_theme_index][9]), LV_PART_MAIN | LV_STATE_DEFAULT);
                            lv_label_set_text(obj, "Porch\nLight");
                        }
                    }
                }
                {
                    // BtnDevice06
                    lv_obj_t *obj = lv_btn_create(parent_obj);
                    objects.btn_device06 = obj;
                    lv_obj_set_pos(obj, 0, 0);
                    lv_obj_set_size(obj, 120, 120);
                    add_style_style_button_default(obj);
                    lv_obj_set_style_align(obj, LV_ALIGN_RIGHT_MID, LV_PART_MAIN | LV_STATE_DEFAULT);
                    {
                        lv_obj_t *parent_obj = obj;
                        {
                            // lblDevice06StatusInd
                            lv_obj_t *obj = lv_label_create(parent_obj);
                            objects.lbl_device06_status_ind = obj;
                            lv_obj_set_pos(obj, 0, 0);
                            lv_obj_set_size(obj, 32, 32);
                            lv_obj_clear_flag(obj, LV_OBJ_FLAG_CLICK_FOCUSABLE|LV_OBJ_FLAG_GESTURE_BUBBLE|LV_OBJ_FLAG_PRESS_LOCK|LV_OBJ_FLAG_SCROLLABLE|LV_OBJ_FLAG_SCROLL_CHAIN_HOR|LV_OBJ_FLAG_SCROLL_CHAIN_VER|LV_OBJ_FLAG_SCROLL_ELASTIC|LV_OBJ_FLAG_SCROLL_MOMENTUM|LV_OBJ_FLAG_SCROLL_WITH_ARROW|LV_OBJ_FLAG_SNAPPABLE);
                            add_style_label_fa32_icon(obj);
                            lv_obj_set_style_align(obj, LV_ALIGN_TOP_MID, LV_PART_MAIN | LV_STATE_DEFAULT);
                            lv_obj_set_style_text_color(obj, lv_color_hex(theme_colors[active_theme_index][9]), LV_PART_MAIN | LV_STATE_DEFAULT);
                            lv_label_set_text(obj, "\uf8ff");
                        }
                        {
                            // lblDevice06Label
                            lv_obj_t *obj = lv_label_create(parent_obj);
                            objects.lbl_device06_label = obj;
                            lv_obj_set_pos(obj, 0, 0);
                            lv_obj_set_size(obj, LV_SIZE_CONTENT, LV_SIZE_CONTENT);
                            lv_obj_clear_flag(obj, LV_OBJ_FLAG_CLICK_FOCUSABLE|LV_OBJ_FLAG_GESTURE_BUBBLE|LV_OBJ_FLAG_PRESS_LOCK|LV_OBJ_FLAG_SCROLLABLE|LV_OBJ_FLAG_SCROLL_CHAIN_HOR|LV_OBJ_FLAG_SCROLL_CHAIN_VER|LV_OBJ_FLAG_SCROLL_ELASTIC|LV_OBJ_FLAG_SCROLL_MOMENTUM|LV_OBJ_FLAG_SCROLL_WITH_ARROW|LV_OBJ_FLAG_SNAPPABLE);
                            add_style_label_default(obj);
                            lv_obj_set_style_align(obj, LV_ALIGN_BOTTOM_MID, LV_PART_MAIN | LV_STATE_DEFAULT);
                            lv_obj_set_style_text_color(obj, lv_color_hex(theme_colors[active_theme_index][9]), LV_PART_MAIN | LV_STATE_DEFAULT);
                            lv_label_set_text(obj, "Trailer\nLights");
                        }
                    }
                }
                {
                    // BtnDevice07
                    lv_obj_t *obj = lv_btn_create(parent_obj);
                    objects.btn_device07 = obj;
                    lv_obj_set_pos(obj, 0, 0);
                    lv_obj_set_size(obj, 120, 120);
                    add_style_style_button_default(obj);
                    lv_obj_set_style_align(obj, LV_ALIGN_BOTTOM_LEFT, LV_PART_MAIN | LV_STATE_DEFAULT);
                    {
                        lv_obj_t *parent_obj = obj;
                        {
                            // lblDevice07StatusInd
                            lv_obj_t *obj = lv_label_create(parent_obj);
                            objects.lbl_device07_status_ind = obj;
                            lv_obj_set_pos(obj, 0, 0);
                            lv_obj_set_size(obj, 32, 32);
                            lv_obj_clear_flag(obj, LV_OBJ_FLAG_CLICK_FOCUSABLE|LV_OBJ_FLAG_GESTURE_BUBBLE|LV_OBJ_FLAG_PRESS_LOCK|LV_OBJ_FLAG_SCROLLABLE|LV_OBJ_FLAG_SCROLL_CHAIN_HOR|LV_OBJ_FLAG_SCROLL_CHAIN_VER|LV_OBJ_FLAG_SCROLL_ELASTIC|LV_OBJ_FLAG_SCROLL_MOMENTUM|LV_OBJ_FLAG_SCROLL_WITH_ARROW|LV_OBJ_FLAG_SNAPPABLE);
                            add_style_label_fa32_icon(obj);
                            lv_obj_set_style_align(obj, LV_ALIGN_TOP_MID, LV_PART_MAIN | LV_STATE_DEFAULT);
                            lv_obj_set_style_text_color(obj, lv_color_hex(theme_colors[active_theme_index][9]), LV_PART_MAIN | LV_STATE_DEFAULT);
                            lv_label_set_text(obj, "\uf773");
                        }
                        {
                            // lblDevice07Label
                            lv_obj_t *obj = lv_label_create(parent_obj);
                            objects.lbl_device07_label = obj;
                            lv_obj_set_pos(obj, 0, 0);
                            lv_obj_set_size(obj, LV_SIZE_CONTENT, LV_SIZE_CONTENT);
                            lv_obj_clear_flag(obj, LV_OBJ_FLAG_CLICK_FOCUSABLE|LV_OBJ_FLAG_GESTURE_BUBBLE|LV_OBJ_FLAG_PRESS_LOCK|LV_OBJ_FLAG_SCROLLABLE|LV_OBJ_FLAG_SCROLL_CHAIN_HOR|LV_OBJ_FLAG_SCROLL_CHAIN_VER|LV_OBJ_FLAG_SCROLL_ELASTIC|LV_OBJ_FLAG_SCROLL_MOMENTUM|LV_OBJ_FLAG_SCROLL_WITH_ARROW|LV_OBJ_FLAG_SNAPPABLE);
                            add_style_label_default(obj);
                            lv_obj_set_style_align(obj, LV_ALIGN_BOTTOM_MID, LV_PART_MAIN | LV_STATE_DEFAULT);
                            lv_obj_set_style_text_color(obj, lv_color_hex(theme_colors[active_theme_index][9]), LV_PART_MAIN | LV_STATE_DEFAULT);
                            lv_label_set_text(obj, "Water\nPump");
                        }
                    }
                }
                {
                    // BtnDevice08
                    lv_obj_t *obj = lv_btn_create(parent_obj);
                    objects.btn_device08 = obj;
                    lv_obj_set_pos(obj, 0, 0);
                    lv_obj_set_size(obj, 120, 120);
                    add_style_style_button_default(obj);
                    lv_obj_set_style_align(obj, LV_ALIGN_BOTTOM_MID, LV_PART_MAIN | LV_STATE_DEFAULT);
                    {
                        lv_obj_t *parent_obj = obj;
                        {
                            // lblDevice08StatusInd
                            lv_obj_t *obj = lv_label_create(parent_obj);
                            objects.lbl_device08_status_ind = obj;
                            lv_obj_set_pos(obj, 0, 0);
                            lv_obj_set_size(obj, 32, 32);
                            lv_obj_clear_flag(obj, LV_OBJ_FLAG_CLICK_FOCUSABLE|LV_OBJ_FLAG_GESTURE_BUBBLE|LV_OBJ_FLAG_PRESS_LOCK|LV_OBJ_FLAG_SCROLLABLE|LV_OBJ_FLAG_SCROLL_CHAIN_HOR|LV_OBJ_FLAG_SCROLL_CHAIN_VER|LV_OBJ_FLAG_SCROLL_ELASTIC|LV_OBJ_FLAG_SCROLL_MOMENTUM|LV_OBJ_FLAG_SCROLL_WITH_ARROW|LV_OBJ_FLAG_SNAPPABLE);
                            add_style_label_fa32_icon(obj);
                            lv_obj_set_style_align(obj, LV_ALIGN_TOP_MID, LV_PART_MAIN | LV_STATE_DEFAULT);
                            lv_obj_set_style_text_color(obj, lv_color_hex(theme_colors[active_theme_index][9]), LV_PART_MAIN | LV_STATE_DEFAULT);
                            lv_label_set_text(obj, "\uf1e6");
                        }
                        {
                            // lblDevice08Label
                            lv_obj_t *obj = lv_label_create(parent_obj);
                            objects.lbl_device08_label = obj;
                            lv_obj_set_pos(obj, 0, 0);
                            lv_obj_set_size(obj, LV_SIZE_CONTENT, LV_SIZE_CONTENT);
                            lv_obj_clear_flag(obj, LV_OBJ_FLAG_CLICK_FOCUSABLE|LV_OBJ_FLAG_GESTURE_BUBBLE|LV_OBJ_FLAG_PRESS_LOCK|LV_OBJ_FLAG_SCROLLABLE|LV_OBJ_FLAG_SCROLL_CHAIN_HOR|LV_OBJ_FLAG_SCROLL_CHAIN_VER|LV_OBJ_FLAG_SCROLL_ELASTIC|LV_OBJ_FLAG_SCROLL_MOMENTUM|LV_OBJ_FLAG_SCROLL_WITH_ARROW|LV_OBJ_FLAG_SNAPPABLE);
                            add_style_label_default(obj);
                            lv_obj_set_style_align(obj, LV_ALIGN_BOTTOM_MID, LV_PART_MAIN | LV_STATE_DEFAULT);
                            lv_obj_set_style_text_color(obj, lv_color_hex(theme_colors[active_theme_index][9]), LV_PART_MAIN | LV_STATE_DEFAULT);
                            lv_label_set_text(obj, "Power\nOutlet");
                        }
                    }
                }
                {
                    lv_obj_t *obj = lv_btn_create(parent_obj);
                    lv_obj_set_pos(obj, 0, 0);
                    lv_obj_set_size(obj, 120, 120);
                    add_style_style_button_default(obj);
                    lv_obj_set_style_align(obj, LV_ALIGN_BOTTOM_RIGHT, LV_PART_MAIN | LV_STATE_DEFAULT);
                    {
                        lv_obj_t *parent_obj = obj;
                        {
                            // lblButtonAllLabel
                            lv_obj_t *obj = lv_label_create(parent_obj);
                            objects.lbl_button_all_label = obj;
                            lv_obj_set_pos(obj, 0, 0);
                            lv_obj_set_size(obj, LV_SIZE_CONTENT, LV_SIZE_CONTENT);
                            lv_obj_clear_flag(obj, LV_OBJ_FLAG_CLICK_FOCUSABLE|LV_OBJ_FLAG_GESTURE_BUBBLE|LV_OBJ_FLAG_PRESS_LOCK|LV_OBJ_FLAG_SCROLLABLE|LV_OBJ_FLAG_SCROLL_CHAIN_HOR|LV_OBJ_FLAG_SCROLL_CHAIN_VER|LV_OBJ_FLAG_SCROLL_ELASTIC|LV_OBJ_FLAG_SCROLL_MOMENTUM|LV_OBJ_FLAG_SCROLL_WITH_ARROW|LV_OBJ_FLAG_SNAPPABLE);
                            add_style_label_default(obj);
                            lv_obj_set_style_align(obj, LV_ALIGN_CENTER, LV_PART_MAIN | LV_STATE_DEFAULT);
                            lv_obj_set_style_text_color(obj, lv_color_hex(theme_colors[active_theme_index][9]), LV_PART_MAIN | LV_STATE_DEFAULT);
                            lv_label_set_text(obj, "All On");
                        }
                    }
                }
            }
        }
        {
            // PanelBrightnessAdjustment
            lv_obj_t *obj = lv_obj_create(parent_obj);
            objects.panel_brightness_adjustment = obj;
            lv_obj_set_pos(obj, 0, 0);
            lv_obj_set_size(obj, LV_PCT(100), LV_PCT(100));
            lv_obj_add_flag(obj, LV_OBJ_FLAG_HIDDEN);
            lv_obj_clear_flag(obj, LV_OBJ_FLAG_CLICK_FOCUSABLE|LV_OBJ_FLAG_GESTURE_BUBBLE|LV_OBJ_FLAG_PRESS_LOCK|LV_OBJ_FLAG_SCROLLABLE|LV_OBJ_FLAG_SCROLL_CHAIN_HOR|LV_OBJ_FLAG_SCROLL_CHAIN_VER|LV_OBJ_FLAG_SCROLL_ELASTIC|LV_OBJ_FLAG_SCROLL_MOMENTUM|LV_OBJ_FLAG_SCROLL_WITH_ARROW|LV_OBJ_FLAG_SNAPPABLE);
            add_style_style_panel_modal_blocker(obj);
            {
                lv_obj_t *parent_obj = obj;
                {
                    lv_obj_t *obj = lv_obj_create(parent_obj);
                    lv_obj_set_pos(obj, 0, 0);
                    lv_obj_set_size(obj, 400, 160);
                    lv_obj_clear_flag(obj, LV_OBJ_FLAG_CLICKABLE|LV_OBJ_FLAG_CLICK_FOCUSABLE|LV_OBJ_FLAG_GESTURE_BUBBLE|LV_OBJ_FLAG_PRESS_LOCK|LV_OBJ_FLAG_SCROLLABLE|LV_OBJ_FLAG_SCROLL_CHAIN_HOR|LV_OBJ_FLAG_SCROLL_CHAIN_VER|LV_OBJ_FLAG_SCROLL_ELASTIC|LV_OBJ_FLAG_SCROLL_MOMENTUM|LV_OBJ_FLAG_SCROLL_WITH_ARROW|LV_OBJ_FLAG_SNAPPABLE);
                    add_style_style_panel_dialog(obj);
                    lv_obj_set_style_align(obj, LV_ALIGN_CENTER, LV_PART_MAIN | LV_STATE_DEFAULT);
                    {
                        lv_obj_t *parent_obj = obj;
                        {
                            lv_obj_t *obj = lv_label_create(parent_obj);
                            lv_obj_set_pos(obj, 0, 10);
                            lv_obj_set_size(obj, LV_SIZE_CONTENT, LV_SIZE_CONTENT);
                            add_style_label_default(obj);
                            lv_obj_set_style_align(obj, LV_ALIGN_TOP_LEFT, LV_PART_MAIN | LV_STATE_DEFAULT);
                            lv_label_set_text(obj, "Brightness");
                        }
                        {
                            // ButtonBrightnessDialogClose
                            lv_obj_t *obj = lv_btn_create(parent_obj);
                            objects.button_brightness_dialog_close = obj;
                            lv_obj_set_pos(obj, 310, -13);
                            lv_obj_set_size(obj, LV_SIZE_CONTENT, LV_SIZE_CONTENT);
                            lv_obj_clear_flag(obj, LV_OBJ_FLAG_CLICK_FOCUSABLE|LV_OBJ_FLAG_GESTURE_BUBBLE|LV_OBJ_FLAG_PRESS_LOCK|LV_OBJ_FLAG_SCROLL_CHAIN_HOR|LV_OBJ_FLAG_SCROLL_CHAIN_VER|LV_OBJ_FLAG_SCROLL_ELASTIC|LV_OBJ_FLAG_SCROLL_MOMENTUM|LV_OBJ_FLAG_SCROLL_ON_FOCUS|LV_OBJ_FLAG_SCROLL_WITH_ARROW|LV_OBJ_FLAG_SNAPPABLE);
                            add_style_button_circle(obj);
                            lv_obj_set_style_radius(obj, 32, LV_PART_MAIN | LV_STATE_DEFAULT);
                            lv_obj_set_style_min_width(obj, 50, LV_PART_MAIN | LV_STATE_DEFAULT);
                            lv_obj_set_style_max_width(obj, 50, LV_PART_MAIN | LV_STATE_DEFAULT);
                            lv_obj_set_style_min_height(obj, 50, LV_PART_MAIN | LV_STATE_DEFAULT);
                            lv_obj_set_style_max_height(obj, 50, LV_PART_MAIN | LV_STATE_DEFAULT);
                            lv_obj_set_style_bg_color(obj, lv_color_hex(theme_colors[active_theme_index][3]), LV_PART_MAIN | LV_STATE_DEFAULT);
                            lv_obj_set_style_text_font(obj, &ui_font_fa32, LV_PART_MAIN | LV_STATE_DEFAULT);
                            lv_obj_set_style_text_color(obj, lv_color_hex(theme_colors[active_theme_index][9]), LV_PART_MAIN | LV_STATE_DEFAULT);
                            {
                                lv_obj_t *parent_obj = obj;
                                {
                                    lv_obj_t *obj = lv_label_create(parent_obj);
                                    objects.obj2 = obj;
                                    lv_obj_set_pos(obj, 0, 0);
                                    lv_obj_set_size(obj, LV_SIZE_CONTENT, LV_SIZE_CONTENT);
                                    add_style_label_circle_button(obj);
                                    lv_obj_set_style_align(obj, LV_ALIGN_CENTER, LV_PART_MAIN | LV_STATE_DEFAULT);
                                    lv_obj_set_style_text_color(obj, lv_color_hex(theme_colors[active_theme_index][9]), LV_PART_MAIN | LV_STATE_DEFAULT);
                                    lv_label_set_text(obj, "\uf057");
                                }
                            }
                        }
                        {
                            // SliderDeviceBrightnessChange
                            lv_obj_t *obj = lv_slider_create(parent_obj);
                            objects.slider_device_brightness_change = obj;
                            lv_obj_set_pos(obj, 0, 65);
                            lv_obj_set_size(obj, LV_PCT(100), 20);
                            lv_slider_set_range(obj, 0, 255);
                            lv_slider_set_value(obj, 128, LV_ANIM_OFF);
                            add_style_style_default_slider(obj);
                        }
                    }
                }
            }
        }
    }
    
    tick_screen_power();
}

void tick_screen_power() {
    tick_user_widget_bottom_nav_bar(52);
}

void create_screen_solar() {
    lv_obj_t *obj = lv_obj_create(0);
    objects.solar = obj;
    lv_obj_set_pos(obj, 0, 0);
    lv_obj_set_size(obj, 800, 480);
    add_style_style_screen_default(obj);
    {
        lv_obj_t *parent_obj = obj;
        {
            // SolarPageBottomNavBar
            lv_obj_t *obj = lv_obj_create(parent_obj);
            objects.solar_page_bottom_nav_bar = obj;
            lv_obj_set_pos(obj, 0, 0);
            lv_obj_set_size(obj, 800, 60);
            lv_obj_set_style_pad_left(obj, 0, LV_PART_MAIN | LV_STATE_DEFAULT);
            lv_obj_set_style_pad_top(obj, 0, LV_PART_MAIN | LV_STATE_DEFAULT);
            lv_obj_set_style_pad_right(obj, 0, LV_PART_MAIN | LV_STATE_DEFAULT);
            lv_obj_set_style_pad_bottom(obj, 0, LV_PART_MAIN | LV_STATE_DEFAULT);
            lv_obj_set_style_bg_opa(obj, 0, LV_PART_MAIN | LV_STATE_DEFAULT);
            lv_obj_set_style_border_width(obj, 0, LV_PART_MAIN | LV_STATE_DEFAULT);
            create_user_widget_bottom_nav_bar(obj, 89);
            lv_obj_set_style_align(obj, LV_ALIGN_BOTTOM_LEFT, LV_PART_MAIN | LV_STATE_DEFAULT);
        }
        {
            // PanelSolarInput
            lv_obj_t *obj = lv_obj_create(parent_obj);
            objects.panel_solar_input = obj;
            lv_obj_set_pos(obj, 11, 15);
            lv_obj_set_size(obj, 224, 149);
            add_style_style_content_panel(obj);
            lv_obj_set_style_align(obj, LV_ALIGN_TOP_LEFT, LV_PART_MAIN | LV_STATE_DEFAULT);
            lv_obj_set_style_bg_color(obj, lv_color_hex(theme_colors[active_theme_index][3]), LV_PART_MAIN | LV_STATE_DEFAULT);
            {
                lv_obj_t *parent_obj = obj;
                {
                    lv_obj_t *obj = lv_label_create(parent_obj);
                    lv_obj_set_pos(obj, 30, 0);
                    lv_obj_set_size(obj, LV_SIZE_CONTENT, LV_SIZE_CONTENT);
                    add_style_label_fa32_icon(obj);
                    lv_obj_set_style_align(obj, LV_ALIGN_TOP_LEFT, LV_PART_MAIN | LV_STATE_DEFAULT);
                    lv_label_set_text(obj, "\uf185");
                }
                {
                    lv_obj_t *obj = lv_label_create(parent_obj);
                    lv_obj_set_pos(obj, 5, 20);
                    lv_obj_set_size(obj, LV_SIZE_CONTENT, LV_SIZE_CONTENT);
                    add_style_label_fa32_icon(obj);
                    lv_obj_set_style_align(obj, LV_ALIGN_TOP_LEFT, LV_PART_MAIN | LV_STATE_DEFAULT);
                    lv_label_set_text(obj, "\uf5ba");
                }
                {
                    // LabelRemainingCacpity_2
                    lv_obj_t *obj = lv_label_create(parent_obj);
                    objects.label_remaining_cacpity_2 = obj;
                    lv_obj_set_pos(obj, 0, 0);
                    lv_obj_set_size(obj, LV_SIZE_CONTENT, LV_SIZE_CONTENT);
                    add_style_label_default(obj);
                    lv_obj_set_style_text_font(obj, &lv_font_montserrat_32, LV_PART_MAIN | LV_STATE_DEFAULT);
                    lv_obj_set_style_align(obj, LV_ALIGN_CENTER, LV_PART_MAIN | LV_STATE_DEFAULT);
                    lv_label_set_text(obj, "0");
                }
                {
                    lv_obj_t *obj = lv_label_create(parent_obj);
                    lv_obj_set_pos(obj, 0, 0);
                    lv_obj_set_size(obj, LV_SIZE_CONTENT, LV_SIZE_CONTENT);
                    add_style_label_nav_text_alternate(obj);
                    lv_obj_set_style_text_font(obj, &lv_font_montserrat_32, LV_PART_MAIN | LV_STATE_DEFAULT);
                    lv_obj_set_style_align(obj, LV_ALIGN_BOTTOM_MID, LV_PART_MAIN | LV_STATE_DEFAULT);
                    lv_label_set_text(obj, "WATTS");
                }
            }
        }
        {
            // PanelChargeType
            lv_obj_t *obj = lv_obj_create(parent_obj);
            objects.panel_charge_type = obj;
            lv_obj_set_pos(obj, 11, -19);
            lv_obj_set_size(obj, 219, 96);
            add_style_style_content_panel(obj);
            lv_obj_set_style_align(obj, LV_ALIGN_LEFT_MID, LV_PART_MAIN | LV_STATE_DEFAULT);
            lv_obj_set_style_bg_color(obj, lv_color_hex(theme_colors[active_theme_index][5]), LV_PART_MAIN | LV_STATE_DEFAULT);
            {
                lv_obj_t *parent_obj = obj;
                {
                    // LabelSolarStatus
                    lv_obj_t *obj = lv_label_create(parent_obj);
                    objects.label_solar_status = obj;
                    lv_obj_set_pos(obj, 43, -1);
                    lv_obj_set_size(obj, LV_SIZE_CONTENT, LV_SIZE_CONTENT);
                    add_style_label_nav_text_alternate(obj);
                    lv_obj_set_style_text_font(obj, &lv_font_montserrat_16, LV_PART_MAIN | LV_STATE_DEFAULT);
                    lv_obj_set_style_align(obj, LV_ALIGN_LEFT_MID, LV_PART_MAIN | LV_STATE_DEFAULT);
                    lv_obj_set_style_text_color(obj, lv_color_hex(theme_colors[active_theme_index][7]), LV_PART_MAIN | LV_STATE_DEFAULT);
                    lv_label_set_text(obj, "BULK CHARGE");
                }
            }
        }
        {
            // PanelShorePower
            lv_obj_t *obj = lv_obj_create(parent_obj);
            objects.panel_shore_power = obj;
            lv_obj_set_pos(obj, 11, -70);
            lv_obj_set_size(obj, 219, 125);
            add_style_style_content_panel(obj);
            lv_obj_set_style_align(obj, LV_ALIGN_BOTTOM_LEFT, LV_PART_MAIN | LV_STATE_DEFAULT);
            lv_obj_set_style_bg_color(obj, lv_color_hex(theme_colors[active_theme_index][4]), LV_PART_MAIN | LV_STATE_DEFAULT);
            {
                lv_obj_t *parent_obj = obj;
                {
                    // LabelPowerShorePowerHeading
                    lv_obj_t *obj = lv_label_create(parent_obj);
                    objects.label_power_shore_power_heading = obj;
                    lv_obj_set_pos(obj, 0, 0);
                    lv_obj_set_size(obj, LV_SIZE_CONTENT, LV_SIZE_CONTENT);
                    add_style_label_default(obj);
                    lv_obj_set_style_text_font(obj, &lv_font_montserrat_14, LV_PART_MAIN | LV_STATE_DEFAULT);
                    lv_obj_set_style_align(obj, LV_ALIGN_TOP_LEFT, LV_PART_MAIN | LV_STATE_DEFAULT);
                    lv_label_set_text(obj, "Shore Power");
                }
                {
                    // LabelShorePowerConnectionStatus
                    lv_obj_t *obj = lv_label_create(parent_obj);
                    objects.label_shore_power_connection_status = obj;
                    lv_obj_set_pos(obj, 0, 0);
                    lv_obj_set_size(obj, LV_SIZE_CONTENT, LV_SIZE_CONTENT);
                    add_style_label_default(obj);
                    lv_obj_set_style_align(obj, LV_ALIGN_BOTTOM_MID, LV_PART_MAIN | LV_STATE_DEFAULT);
                    lv_label_set_text(obj, "Not Connected");
                }
                {
                    // PanelShorePowerIndicatorBackground
                    lv_obj_t *obj = lv_obj_create(parent_obj);
                    objects.panel_shore_power_indicator_background = obj;
                    lv_obj_set_pos(obj, 0, 0);
                    lv_obj_set_size(obj, 60, 60);
                    lv_obj_clear_flag(obj, LV_OBJ_FLAG_CLICKABLE|LV_OBJ_FLAG_CLICK_FOCUSABLE|LV_OBJ_FLAG_GESTURE_BUBBLE|LV_OBJ_FLAG_PRESS_LOCK|LV_OBJ_FLAG_SCROLLABLE|LV_OBJ_FLAG_SCROLL_CHAIN_HOR|LV_OBJ_FLAG_SCROLL_CHAIN_VER|LV_OBJ_FLAG_SCROLL_ELASTIC|LV_OBJ_FLAG_SCROLL_MOMENTUM|LV_OBJ_FLAG_SCROLL_WITH_ARROW|LV_OBJ_FLAG_SNAPPABLE);
                    add_style_style_panel_default(obj);
                    lv_obj_set_style_align(obj, LV_ALIGN_CENTER, LV_PART_MAIN | LV_STATE_DEFAULT);
                    lv_obj_set_style_radius(obj, 30, LV_PART_MAIN | LV_STATE_DEFAULT);
                    lv_obj_set_style_bg_color(obj, lv_color_hex(theme_colors[active_theme_index][3]), LV_PART_MAIN | LV_STATE_DEFAULT);
                    lv_obj_set_style_text_color(obj, lv_color_hex(theme_colors[active_theme_index][7]), LV_PART_MAIN | LV_STATE_DEFAULT);
                    lv_obj_set_style_bg_color(obj, lv_color_hex(theme_colors[active_theme_index][5]), LV_PART_MAIN | LV_STATE_CHECKED);
                    {
                        lv_obj_t *parent_obj = obj;
                        {
                            // PanelShorePowerIndicatorForeground
                            lv_obj_t *obj = lv_label_create(parent_obj);
                            objects.panel_shore_power_indicator_foreground = obj;
                            lv_obj_set_pos(obj, 0, 0);
                            lv_obj_set_size(obj, LV_SIZE_CONTENT, LV_SIZE_CONTENT);
                            add_style_label_fa32_icon(obj);
                            lv_obj_set_style_align(obj, LV_ALIGN_CENTER, LV_PART_MAIN | LV_STATE_DEFAULT);
                            lv_obj_set_style_text_color(obj, lv_color_hex(theme_colors[active_theme_index][0]), LV_PART_MAIN | LV_STATE_CHECKED);
                            lv_label_set_text(obj, "\uf1e6");
                        }
                    }
                }
            }
        }
        {
            // PanelPowerBatteryStats
            lv_obj_t *obj = lv_obj_create(parent_obj);
            objects.panel_power_battery_stats = obj;
            lv_obj_set_pos(obj, -39, 15);
            lv_obj_set_size(obj, 223, 395);
            lv_obj_clear_flag(obj, LV_OBJ_FLAG_CLICKABLE|LV_OBJ_FLAG_CLICK_FOCUSABLE|LV_OBJ_FLAG_GESTURE_BUBBLE|LV_OBJ_FLAG_PRESS_LOCK|LV_OBJ_FLAG_SCROLLABLE|LV_OBJ_FLAG_SCROLL_CHAIN_HOR|LV_OBJ_FLAG_SCROLL_CHAIN_VER|LV_OBJ_FLAG_SCROLL_ELASTIC|LV_OBJ_FLAG_SCROLL_MOMENTUM|LV_OBJ_FLAG_SCROLL_WITH_ARROW|LV_OBJ_FLAG_SNAPPABLE);
            add_style_style_content_panel(obj);
            lv_obj_set_style_align(obj, LV_ALIGN_TOP_MID, LV_PART_MAIN | LV_STATE_DEFAULT);
            lv_obj_set_style_bg_color(obj, lv_color_hex(theme_colors[active_theme_index][3]), LV_PART_MAIN | LV_STATE_DEFAULT);
            {
                lv_obj_t *parent_obj = obj;
                {
                    // LabelPowerRemainingCacpity_1
                    lv_obj_t *obj = lv_label_create(parent_obj);
                    objects.label_power_remaining_cacpity_1 = obj;
                    lv_obj_set_pos(obj, 0, 0);
                    lv_obj_set_size(obj, LV_SIZE_CONTENT, LV_SIZE_CONTENT);
                    add_style_label_default(obj);
                    lv_obj_set_style_text_font(obj, &lv_font_montserrat_22, LV_PART_MAIN | LV_STATE_DEFAULT);
                    lv_obj_set_style_align(obj, LV_ALIGN_TOP_LEFT, LV_PART_MAIN | LV_STATE_DEFAULT);
                    lv_label_set_text(obj, "Battery Status");
                }
                {
                    // BarBatterySoc
                    lv_obj_t *obj = lv_bar_create(parent_obj);
                    objects.bar_battery_soc = obj;
                    lv_obj_set_pos(obj, 0, 0);
                    lv_obj_set_size(obj, 150, 256);
                    add_style_bar_default(obj);
                    lv_obj_set_style_radius(obj, 25, LV_PART_MAIN | LV_STATE_DEFAULT);
                    lv_obj_set_style_outline_width(obj, 3, LV_PART_MAIN | LV_STATE_DEFAULT);
                    lv_obj_set_style_outline_color(obj, lv_color_hex(theme_colors[active_theme_index][5]), LV_PART_MAIN | LV_STATE_DEFAULT);
                    lv_obj_set_style_align(obj, LV_ALIGN_CENTER, LV_PART_MAIN | LV_STATE_DEFAULT);
                    lv_obj_set_style_pad_bottom(obj, 3, LV_PART_MAIN | LV_STATE_DEFAULT);
                    lv_obj_set_style_pad_top(obj, 3, LV_PART_MAIN | LV_STATE_DEFAULT);
                    lv_obj_set_style_pad_left(obj, 3, LV_PART_MAIN | LV_STATE_DEFAULT);
                    lv_obj_set_style_pad_right(obj, 3, LV_PART_MAIN | LV_STATE_DEFAULT);
                    lv_obj_set_style_radius(obj, 25, LV_PART_INDICATOR | LV_STATE_DEFAULT);
                    lv_obj_set_style_bg_color(obj, lv_color_hex(theme_colors[active_theme_index][5]), LV_PART_INDICATOR | LV_STATE_DEFAULT);
                    lv_obj_set_style_outline_width(obj, 0, LV_PART_INDICATOR | LV_STATE_DEFAULT);
                    {
                        lv_obj_t *parent_obj = obj;
                        {
                            // LabelPowerBatteryPercentage
                            lv_obj_t *obj = lv_label_create(parent_obj);
                            objects.label_power_battery_percentage = obj;
                            lv_obj_set_pos(obj, -10, -20);
                            lv_obj_set_size(obj, LV_SIZE_CONTENT, LV_SIZE_CONTENT);
                            add_style_label_default(obj);
                            lv_obj_set_style_align(obj, LV_ALIGN_CENTER, LV_PART_MAIN | LV_STATE_DEFAULT);
                            lv_obj_set_style_text_color(obj, lv_color_hex(theme_colors[active_theme_index][7]), LV_PART_MAIN | LV_STATE_DEFAULT);
                            lv_obj_set_style_text_font(obj, &lv_font_montserrat_32, LV_PART_MAIN | LV_STATE_DEFAULT);
                            lv_label_set_text(obj, "0");
                        }
                        {
                            // LabelBatteryVoltage
                            lv_obj_t *obj = lv_label_create(parent_obj);
                            objects.label_battery_voltage = obj;
                            lv_obj_set_pos(obj, -10, 30);
                            lv_obj_set_size(obj, LV_SIZE_CONTENT, LV_SIZE_CONTENT);
                            add_style_label_default(obj);
                            lv_obj_set_style_align(obj, LV_ALIGN_CENTER, LV_PART_MAIN | LV_STATE_DEFAULT);
                            lv_obj_set_style_text_color(obj, lv_color_hex(theme_colors[active_theme_index][7]), LV_PART_MAIN | LV_STATE_DEFAULT);
                            lv_obj_set_style_text_font(obj, &lv_font_montserrat_32, LV_PART_MAIN | LV_STATE_DEFAULT);
                            lv_label_set_text(obj, "0");
                        }
                    }
                }
                {
                    lv_obj_t *obj = lv_label_create(parent_obj);
                    lv_obj_set_pos(obj, 47, -142);
                    lv_obj_set_size(obj, LV_SIZE_CONTENT, LV_SIZE_CONTENT);
                    add_style_label_nav_text_alternate(obj);
                    lv_obj_set_style_text_font(obj, &lv_font_montserrat_32, LV_PART_MAIN | LV_STATE_DEFAULT);
                    lv_obj_set_style_align(obj, LV_ALIGN_BOTTOM_MID, LV_PART_MAIN | LV_STATE_DEFAULT);
                    lv_label_set_text(obj, "V");
                }
            }
        }
        {
            // PanelPowerRemainingTime
            lv_obj_t *obj = lv_obj_create(parent_obj);
            objects.panel_power_remaining_time = obj;
            lv_obj_set_pos(obj, 488, 15);
            lv_obj_set_size(obj, 296, 392);
            lv_obj_clear_flag(obj, LV_OBJ_FLAG_CLICKABLE|LV_OBJ_FLAG_CLICK_FOCUSABLE|LV_OBJ_FLAG_GESTURE_BUBBLE|LV_OBJ_FLAG_PRESS_LOCK|LV_OBJ_FLAG_SCROLLABLE|LV_OBJ_FLAG_SCROLL_CHAIN_HOR|LV_OBJ_FLAG_SCROLL_CHAIN_VER|LV_OBJ_FLAG_SCROLL_ELASTIC|LV_OBJ_FLAG_SCROLL_MOMENTUM|LV_OBJ_FLAG_SCROLL_WITH_ARROW|LV_OBJ_FLAG_SNAPPABLE);
            add_style_style_content_panel(obj);
            lv_obj_set_style_bg_color(obj, lv_color_hex(theme_colors[active_theme_index][3]), LV_PART_MAIN | LV_STATE_DEFAULT);
            {
                lv_obj_t *parent_obj = obj;
                {
                    // LabelPowerRemainingCacpity
                    lv_obj_t *obj = lv_label_create(parent_obj);
                    objects.label_power_remaining_cacpity = obj;
                    lv_obj_set_pos(obj, 0, 0);
                    lv_obj_set_size(obj, LV_SIZE_CONTENT, LV_SIZE_CONTENT);
                    add_style_label_default(obj);
                    lv_obj_set_style_text_font(obj, &lv_font_montserrat_22, LV_PART_MAIN | LV_STATE_DEFAULT);
                    lv_label_set_text(obj, "Battery Consumption");
                }
                {
                    // PowerRemainingArcGroup
                    lv_obj_t *obj = lv_obj_create(parent_obj);
                    objects.power_remaining_arc_group = obj;
                    lv_obj_set_pos(obj, 15, 31);
                    lv_obj_set_size(obj, 258, 257);
                    lv_obj_clear_flag(obj, LV_OBJ_FLAG_CLICKABLE|LV_OBJ_FLAG_CLICK_FOCUSABLE|LV_OBJ_FLAG_GESTURE_BUBBLE|LV_OBJ_FLAG_PRESS_LOCK|LV_OBJ_FLAG_SCROLLABLE|LV_OBJ_FLAG_SCROLL_CHAIN_HOR|LV_OBJ_FLAG_SCROLL_CHAIN_VER|LV_OBJ_FLAG_SCROLL_ELASTIC|LV_OBJ_FLAG_SCROLL_MOMENTUM|LV_OBJ_FLAG_SCROLL_WITH_ARROW|LV_OBJ_FLAG_SNAPPABLE);
                    add_style_style_panel_default(obj);
                    lv_obj_set_style_align(obj, LV_ALIGN_TOP_LEFT, LV_PART_MAIN | LV_STATE_DEFAULT);
                    lv_obj_set_style_bg_opa(obj, 0, LV_PART_MAIN | LV_STATE_DEFAULT);
                    lv_obj_set_style_bg_color(obj, lv_color_hex(0xffffffff), LV_PART_MAIN | LV_STATE_DEFAULT);
                    lv_obj_set_style_border_width(obj, 0, LV_PART_MAIN | LV_STATE_DEFAULT);
                    {
                        lv_obj_t *parent_obj = obj;
                        {
                            // PowerArcRemainingHours
                            lv_obj_t *obj = lv_arc_create(parent_obj);
                            objects.power_arc_remaining_hours = obj;
                            lv_obj_set_pos(obj, 0, 0);
                            lv_obj_set_size(obj, 250, 250);
                            lv_arc_set_range(obj, 0, 2000);
                            lv_arc_set_value(obj, 200);
                            add_style_arc_default(obj);
                            lv_obj_set_style_bg_opa(obj, 0, LV_PART_KNOB | LV_STATE_DEFAULT);
                            lv_obj_set_style_bg_color(obj, lv_color_hex(theme_colors[active_theme_index][0]), LV_PART_KNOB | LV_STATE_DEFAULT);
                            lv_obj_set_style_arc_width(obj, 20, LV_PART_INDICATOR | LV_STATE_DEFAULT);
                            lv_obj_set_style_arc_color(obj, lv_color_hex(theme_colors[active_theme_index][0]), LV_PART_INDICATOR | LV_STATE_DEFAULT);
                            lv_obj_set_style_arc_width(obj, 25, LV_PART_MAIN | LV_STATE_DEFAULT);
                            lv_obj_set_style_arc_color(obj, lv_color_hex(0xff635c5c), LV_PART_MAIN | LV_STATE_DEFAULT);
                            lv_obj_set_style_bg_color(obj, lv_color_hex(0xff746e6e), LV_PART_MAIN | LV_STATE_DEFAULT);
                            lv_obj_set_style_bg_opa(obj, 255, LV_PART_MAIN | LV_STATE_DEFAULT);
                            lv_obj_set_style_radius(obj, 250, LV_PART_MAIN | LV_STATE_DEFAULT);
                            lv_obj_set_style_pad_top(obj, 10, LV_PART_MAIN | LV_STATE_DEFAULT);
                            lv_obj_set_style_pad_bottom(obj, 10, LV_PART_MAIN | LV_STATE_DEFAULT);
                            lv_obj_set_style_pad_left(obj, 10, LV_PART_MAIN | LV_STATE_DEFAULT);
                            lv_obj_set_style_pad_right(obj, 10, LV_PART_MAIN | LV_STATE_DEFAULT);
                            lv_obj_set_style_align(obj, LV_ALIGN_CENTER, LV_PART_MAIN | LV_STATE_DEFAULT);
                            lv_obj_set_style_border_opa(obj, 255, LV_PART_MAIN | LV_STATE_DEFAULT);
                            lv_obj_set_style_border_color(obj, lv_color_hex(0xff625d5d), LV_PART_MAIN | LV_STATE_DEFAULT);
                            lv_obj_set_style_border_width(obj, 3, LV_PART_MAIN | LV_STATE_DEFAULT);
                        }
                        {
                            // PanelPowerRemainingCenter
                            lv_obj_t *obj = lv_obj_create(parent_obj);
                            objects.panel_power_remaining_center = obj;
                            lv_obj_set_pos(obj, 0, 0);
                            lv_obj_set_size(obj, 180, 180);
                            lv_obj_clear_flag(obj, LV_OBJ_FLAG_CLICKABLE|LV_OBJ_FLAG_CLICK_FOCUSABLE|LV_OBJ_FLAG_GESTURE_BUBBLE|LV_OBJ_FLAG_PRESS_LOCK|LV_OBJ_FLAG_SCROLLABLE|LV_OBJ_FLAG_SCROLL_CHAIN_HOR|LV_OBJ_FLAG_SCROLL_CHAIN_VER|LV_OBJ_FLAG_SCROLL_ELASTIC|LV_OBJ_FLAG_SCROLL_MOMENTUM|LV_OBJ_FLAG_SCROLL_WITH_ARROW|LV_OBJ_FLAG_SNAPPABLE);
                            add_style_style_panel_default(obj);
                            lv_obj_set_style_align(obj, LV_ALIGN_CENTER, LV_PART_MAIN | LV_STATE_DEFAULT);
                            lv_obj_set_style_radius(obj, 300, LV_PART_MAIN | LV_STATE_DEFAULT);
                            lv_obj_set_style_bg_color(obj, lv_color_hex(0xff7c7777), LV_PART_MAIN | LV_STATE_DEFAULT);
                        }
                        {
                            // LabelTimeToGoMeasurementType
                            lv_obj_t *obj = lv_label_create(parent_obj);
                            objects.label_time_to_go_measurement_type = obj;
                            lv_obj_set_pos(obj, -43, -1);
                            lv_obj_set_size(obj, LV_SIZE_CONTENT, LV_SIZE_CONTENT);
                            add_style_label_nav_text_alternate(obj);
                            lv_obj_set_style_align(obj, LV_ALIGN_RIGHT_MID, LV_PART_MAIN | LV_STATE_DEFAULT);
                            lv_obj_set_style_text_font(obj, &lv_font_montserrat_32, LV_PART_MAIN | LV_STATE_DEFAULT);
                            lv_label_set_text(obj, "Hrs");
                        }
                        {
                            // LabelPowerRemainingTimeToGoValue
                            lv_obj_t *obj = lv_label_create(parent_obj);
                            objects.label_power_remaining_time_to_go_value = obj;
                            lv_obj_set_pos(obj, -32, 0);
                            lv_obj_set_size(obj, LV_SIZE_CONTENT, LV_SIZE_CONTENT);
                            lv_obj_clear_flag(obj, LV_OBJ_FLAG_CLICK_FOCUSABLE|LV_OBJ_FLAG_GESTURE_BUBBLE|LV_OBJ_FLAG_PRESS_LOCK|LV_OBJ_FLAG_SCROLLABLE|LV_OBJ_FLAG_SCROLL_CHAIN_HOR|LV_OBJ_FLAG_SCROLL_CHAIN_VER|LV_OBJ_FLAG_SCROLL_ELASTIC|LV_OBJ_FLAG_SCROLL_MOMENTUM|LV_OBJ_FLAG_SCROLL_WITH_ARROW|LV_OBJ_FLAG_SNAPPABLE);
                            add_style_style_top_nav_text_normal(obj);
                            lv_obj_set_style_align(obj, LV_ALIGN_CENTER, LV_PART_MAIN | LV_STATE_DEFAULT);
                            lv_obj_set_style_pad_top(obj, 0, LV_PART_MAIN | LV_STATE_DEFAULT);
                            lv_label_set_text(obj, "0");
                        }
                        {
                            // LabelPowerRemaining
                            lv_obj_t *obj = lv_label_create(parent_obj);
                            objects.label_power_remaining = obj;
                            lv_obj_set_pos(obj, 0, -60);
                            lv_obj_set_size(obj, LV_SIZE_CONTENT, LV_SIZE_CONTENT);
                            lv_obj_clear_flag(obj, LV_OBJ_FLAG_CLICK_FOCUSABLE|LV_OBJ_FLAG_GESTURE_BUBBLE|LV_OBJ_FLAG_PRESS_LOCK|LV_OBJ_FLAG_SCROLLABLE|LV_OBJ_FLAG_SCROLL_CHAIN_HOR|LV_OBJ_FLAG_SCROLL_CHAIN_VER|LV_OBJ_FLAG_SCROLL_ELASTIC|LV_OBJ_FLAG_SCROLL_MOMENTUM|LV_OBJ_FLAG_SCROLL_WITH_ARROW|LV_OBJ_FLAG_SNAPPABLE);
                            add_style_label_default(obj);
                            lv_obj_set_style_align(obj, LV_ALIGN_BOTTOM_MID, LV_PART_MAIN | LV_STATE_DEFAULT);
                            lv_label_set_text(obj, "Remaining");
                        }
                    }
                }
                {
                    // LabelRemainingCacpity_1
                    lv_obj_t *obj = lv_label_create(parent_obj);
                    objects.label_remaining_cacpity_1 = obj;
                    lv_obj_set_pos(obj, -50, -5);
                    lv_obj_set_size(obj, LV_SIZE_CONTENT, LV_SIZE_CONTENT);
                    add_style_label_default(obj);
                    lv_obj_set_style_text_font(obj, &lv_font_montserrat_32, LV_PART_MAIN | LV_STATE_DEFAULT);
                    lv_obj_set_style_align(obj, LV_ALIGN_BOTTOM_MID, LV_PART_MAIN | LV_STATE_DEFAULT);
                    lv_obj_set_style_text_align(obj, LV_TEXT_ALIGN_RIGHT, LV_PART_MAIN | LV_STATE_DEFAULT);
                    lv_label_set_text(obj, "");
                }
                {
                    lv_obj_t *obj = lv_label_create(parent_obj);
                    lv_obj_set_pos(obj, 50, -5);
                    lv_obj_set_size(obj, LV_SIZE_CONTENT, LV_SIZE_CONTENT);
                    add_style_label_nav_text_alternate(obj);
                    lv_obj_set_style_text_font(obj, &lv_font_montserrat_32, LV_PART_MAIN | LV_STATE_DEFAULT);
                    lv_obj_set_style_align(obj, LV_ALIGN_BOTTOM_MID, LV_PART_MAIN | LV_STATE_DEFAULT);
                    lv_obj_set_style_text_align(obj, LV_TEXT_ALIGN_LEFT, LV_PART_MAIN | LV_STATE_DEFAULT);
                    lv_label_set_text(obj, "WATTS");
                }
            }
        }
        {
            lv_obj_t *obj = lv_label_create(parent_obj);
            objects.obj3 = obj;
            lv_obj_set_pos(obj, 381, 175);
            lv_obj_set_size(obj, LV_SIZE_CONTENT, LV_SIZE_CONTENT);
            add_style_label_default(obj);
            lv_obj_set_style_text_font(obj, &lv_font_montserrat_32, LV_PART_MAIN | LV_STATE_DEFAULT);
            lv_obj_set_style_text_color(obj, lv_color_hex(theme_colors[active_theme_index][7]), LV_PART_MAIN | LV_STATE_DEFAULT);
            lv_label_set_text(obj, "%");
        }
    }
    
    tick_screen_solar();
}

void tick_screen_solar() {
    tick_user_widget_bottom_nav_bar(89);
    {
        const char *new_val = get_var_current_power_consumption_in_watts();
        const char *cur_val = lv_label_get_text(objects.label_remaining_cacpity_1);
        if (strcmp(new_val, cur_val) != 0) {
            tick_value_change_obj = objects.label_remaining_cacpity_1;
            lv_label_set_text(objects.label_remaining_cacpity_1, new_val);
            tick_value_change_obj = NULL;
        }
    }
}

void create_screen_air() {
    lv_obj_t *obj = lv_obj_create(0);
    objects.air = obj;
    lv_obj_set_pos(obj, 0, 0);
    lv_obj_set_size(obj, 800, 480);
    add_style_style_screen_default(obj);
    {
        lv_obj_t *parent_obj = obj;
        {
            // AirPageBottomNavBar
            lv_obj_t *obj = lv_obj_create(parent_obj);
            objects.air_page_bottom_nav_bar = obj;
            lv_obj_set_pos(obj, 0, 0);
            lv_obj_set_size(obj, 800, 60);
            lv_obj_set_style_pad_left(obj, 0, LV_PART_MAIN | LV_STATE_DEFAULT);
            lv_obj_set_style_pad_top(obj, 0, LV_PART_MAIN | LV_STATE_DEFAULT);
            lv_obj_set_style_pad_right(obj, 0, LV_PART_MAIN | LV_STATE_DEFAULT);
            lv_obj_set_style_pad_bottom(obj, 0, LV_PART_MAIN | LV_STATE_DEFAULT);
            lv_obj_set_style_bg_opa(obj, 0, LV_PART_MAIN | LV_STATE_DEFAULT);
            lv_obj_set_style_border_width(obj, 0, LV_PART_MAIN | LV_STATE_DEFAULT);
            create_user_widget_bottom_nav_bar(obj, 120);
            lv_obj_set_style_align(obj, LV_ALIGN_BOTTOM_LEFT, LV_PART_MAIN | LV_STATE_DEFAULT);
        }
        {
            lv_obj_t *obj = lv_obj_create(parent_obj);
            objects.obj4 = obj;
            lv_obj_set_pos(obj, 10, 16);
            lv_obj_set_size(obj, 373, 391);
            add_style_style_content_panel(obj);
            lv_obj_set_style_bg_color(obj, lv_color_hex(theme_colors[active_theme_index][3]), LV_PART_MAIN | LV_STATE_DEFAULT);
            {
                lv_obj_t *parent_obj = obj;
                {
                    // LabelRelativeHumidityHeader_1
                    lv_obj_t *obj = lv_label_create(parent_obj);
                    objects.label_relative_humidity_header_1 = obj;
                    lv_obj_set_pos(obj, 0, 0);
                    lv_obj_set_size(obj, LV_SIZE_CONTENT, LV_SIZE_CONTENT);
                    add_style_label_default(obj);
                    lv_obj_set_style_text_font(obj, &lv_font_montserrat_22, LV_PART_MAIN | LV_STATE_DEFAULT);
                    lv_label_set_text(obj, "Interior Temperature");
                }
                {
                    // BarInteriorTemperature
                    lv_obj_t *obj = lv_bar_create(parent_obj);
                    objects.bar_interior_temperature = obj;
                    lv_obj_set_pos(obj, 0, 0);
                    lv_obj_set_size(obj, 150, 256);
                    lv_bar_set_range(obj, 0, 120);
                    add_style_bar_default(obj);
                    lv_obj_set_style_radius(obj, 25, LV_PART_MAIN | LV_STATE_DEFAULT);
                    lv_obj_set_style_outline_width(obj, 3, LV_PART_MAIN | LV_STATE_DEFAULT);
                    lv_obj_set_style_outline_color(obj, lv_color_hex(theme_colors[active_theme_index][5]), LV_PART_MAIN | LV_STATE_DEFAULT);
                    lv_obj_set_style_align(obj, LV_ALIGN_CENTER, LV_PART_MAIN | LV_STATE_DEFAULT);
                    lv_obj_set_style_pad_bottom(obj, 3, LV_PART_MAIN | LV_STATE_DEFAULT);
                    lv_obj_set_style_pad_top(obj, 3, LV_PART_MAIN | LV_STATE_DEFAULT);
                    lv_obj_set_style_pad_left(obj, 3, LV_PART_MAIN | LV_STATE_DEFAULT);
                    lv_obj_set_style_pad_right(obj, 3, LV_PART_MAIN | LV_STATE_DEFAULT);
                    lv_obj_set_style_radius(obj, 25, LV_PART_INDICATOR | LV_STATE_DEFAULT);
                    lv_obj_set_style_bg_color(obj, lv_color_hex(theme_colors[active_theme_index][5]), LV_PART_INDICATOR | LV_STATE_DEFAULT);
                    lv_obj_set_style_outline_width(obj, 0, LV_PART_INDICATOR | LV_STATE_DEFAULT);
                    {
                        lv_obj_t *parent_obj = obj;
                        {
                            // LabelInteriorTempValue
                            lv_obj_t *obj = lv_label_create(parent_obj);
                            objects.label_interior_temp_value = obj;
                            lv_obj_set_pos(obj, 0, -20);
                            lv_obj_set_size(obj, LV_SIZE_CONTENT, LV_SIZE_CONTENT);
                            add_style_label_default(obj);
                            lv_obj_set_style_align(obj, LV_ALIGN_CENTER, LV_PART_MAIN | LV_STATE_DEFAULT);
                            lv_obj_set_style_text_color(obj, lv_color_hex(theme_colors[active_theme_index][7]), LV_PART_MAIN | LV_STATE_DEFAULT);
                            lv_obj_set_style_text_font(obj, &lv_font_montserrat_32, LV_PART_MAIN | LV_STATE_DEFAULT);
                            lv_label_set_text(obj, "0");
                        }
                        {
                            // LabelAirQualityTempReadingTypeLabel
                            lv_obj_t *obj = lv_label_create(parent_obj);
                            objects.label_air_quality_temp_reading_type_label = obj;
                            lv_obj_set_pos(obj, 0, 30);
                            lv_obj_set_size(obj, LV_SIZE_CONTENT, LV_SIZE_CONTENT);
                            add_style_label_default(obj);
                            lv_obj_set_style_align(obj, LV_ALIGN_CENTER, LV_PART_MAIN | LV_STATE_DEFAULT);
                            lv_obj_set_style_text_color(obj, lv_color_hex(theme_colors[active_theme_index][7]), LV_PART_MAIN | LV_STATE_DEFAULT);
                            lv_obj_set_style_text_font(obj, &lv_font_montserrat_32, LV_PART_MAIN | LV_STATE_DEFAULT);
                            lv_label_set_text(obj, "F");
                        }
                    }
                }
            }
        }
        {
            // PanelRelativeHumity
            lv_obj_t *obj = lv_obj_create(parent_obj);
            objects.panel_relative_humity = obj;
            lv_obj_set_pos(obj, 400, 16);
            lv_obj_set_size(obj, 384, 391);
            lv_obj_clear_flag(obj, LV_OBJ_FLAG_CLICKABLE|LV_OBJ_FLAG_CLICK_FOCUSABLE|LV_OBJ_FLAG_GESTURE_BUBBLE|LV_OBJ_FLAG_PRESS_LOCK|LV_OBJ_FLAG_SCROLLABLE|LV_OBJ_FLAG_SCROLL_CHAIN_HOR|LV_OBJ_FLAG_SCROLL_CHAIN_VER|LV_OBJ_FLAG_SCROLL_ELASTIC|LV_OBJ_FLAG_SCROLL_MOMENTUM|LV_OBJ_FLAG_SCROLL_WITH_ARROW|LV_OBJ_FLAG_SNAPPABLE);
            add_style_style_content_panel(obj);
            lv_obj_set_style_bg_color(obj, lv_color_hex(theme_colors[active_theme_index][3]), LV_PART_MAIN | LV_STATE_DEFAULT);
            {
                lv_obj_t *parent_obj = obj;
                {
                    // LabelRelativeHumidityHeader
                    lv_obj_t *obj = lv_label_create(parent_obj);
                    objects.label_relative_humidity_header = obj;
                    lv_obj_set_pos(obj, 0, 0);
                    lv_obj_set_size(obj, LV_SIZE_CONTENT, LV_SIZE_CONTENT);
                    add_style_label_default(obj);
                    lv_obj_set_style_text_font(obj, &lv_font_montserrat_22, LV_PART_MAIN | LV_STATE_DEFAULT);
                    lv_label_set_text(obj, "Relative Humidity");
                }
                {
                    // RelativeHumidityArcGroup
                    lv_obj_t *obj = lv_obj_create(parent_obj);
                    objects.relative_humidity_arc_group = obj;
                    lv_obj_set_pos(obj, 37, 62);
                    lv_obj_set_size(obj, 300, 300);
                    lv_obj_clear_flag(obj, LV_OBJ_FLAG_CLICKABLE|LV_OBJ_FLAG_CLICK_FOCUSABLE|LV_OBJ_FLAG_GESTURE_BUBBLE|LV_OBJ_FLAG_PRESS_LOCK|LV_OBJ_FLAG_SCROLLABLE|LV_OBJ_FLAG_SCROLL_CHAIN_HOR|LV_OBJ_FLAG_SCROLL_CHAIN_VER|LV_OBJ_FLAG_SCROLL_ELASTIC|LV_OBJ_FLAG_SCROLL_MOMENTUM|LV_OBJ_FLAG_SCROLL_WITH_ARROW|LV_OBJ_FLAG_SNAPPABLE);
                    add_style_style_panel_default(obj);
                    lv_obj_set_style_align(obj, LV_ALIGN_TOP_LEFT, LV_PART_MAIN | LV_STATE_DEFAULT);
                    lv_obj_set_style_bg_opa(obj, 0, LV_PART_MAIN | LV_STATE_DEFAULT);
                    lv_obj_set_style_bg_color(obj, lv_color_hex(0xffffffff), LV_PART_MAIN | LV_STATE_DEFAULT);
                    lv_obj_set_style_border_width(obj, 0, LV_PART_MAIN | LV_STATE_DEFAULT);
                    {
                        lv_obj_t *parent_obj = obj;
                        {
                            // ArcRelativeHumidity
                            lv_obj_t *obj = lv_arc_create(parent_obj);
                            objects.arc_relative_humidity = obj;
                            lv_obj_set_pos(obj, 0, 0);
                            lv_obj_set_size(obj, 250, 250);
                            lv_arc_set_value(obj, 0);
                            add_style_arc_default(obj);
                            lv_obj_set_style_bg_opa(obj, 0, LV_PART_KNOB | LV_STATE_DEFAULT);
                            lv_obj_set_style_bg_color(obj, lv_color_hex(theme_colors[active_theme_index][0]), LV_PART_KNOB | LV_STATE_DEFAULT);
                            lv_obj_set_style_arc_width(obj, 20, LV_PART_INDICATOR | LV_STATE_DEFAULT);
                            lv_obj_set_style_arc_color(obj, lv_color_hex(theme_colors[active_theme_index][0]), LV_PART_INDICATOR | LV_STATE_DEFAULT);
                            lv_obj_set_style_arc_width(obj, 25, LV_PART_MAIN | LV_STATE_DEFAULT);
                            lv_obj_set_style_arc_color(obj, lv_color_hex(0xff635c5c), LV_PART_MAIN | LV_STATE_DEFAULT);
                            lv_obj_set_style_bg_color(obj, lv_color_hex(0xff746e6e), LV_PART_MAIN | LV_STATE_DEFAULT);
                            lv_obj_set_style_bg_opa(obj, 255, LV_PART_MAIN | LV_STATE_DEFAULT);
                            lv_obj_set_style_radius(obj, 250, LV_PART_MAIN | LV_STATE_DEFAULT);
                            lv_obj_set_style_pad_top(obj, 10, LV_PART_MAIN | LV_STATE_DEFAULT);
                            lv_obj_set_style_pad_bottom(obj, 10, LV_PART_MAIN | LV_STATE_DEFAULT);
                            lv_obj_set_style_pad_left(obj, 10, LV_PART_MAIN | LV_STATE_DEFAULT);
                            lv_obj_set_style_pad_right(obj, 10, LV_PART_MAIN | LV_STATE_DEFAULT);
                            lv_obj_set_style_align(obj, LV_ALIGN_CENTER, LV_PART_MAIN | LV_STATE_DEFAULT);
                            lv_obj_set_style_border_opa(obj, 255, LV_PART_MAIN | LV_STATE_DEFAULT);
                            lv_obj_set_style_border_color(obj, lv_color_hex(0xff625d5d), LV_PART_MAIN | LV_STATE_DEFAULT);
                            lv_obj_set_style_border_width(obj, 3, LV_PART_MAIN | LV_STATE_DEFAULT);
                        }
                        {
                            // PanelRelativeHumidityCenter
                            lv_obj_t *obj = lv_obj_create(parent_obj);
                            objects.panel_relative_humidity_center = obj;
                            lv_obj_set_pos(obj, 0, 0);
                            lv_obj_set_size(obj, 180, 180);
                            lv_obj_clear_flag(obj, LV_OBJ_FLAG_CLICKABLE|LV_OBJ_FLAG_CLICK_FOCUSABLE|LV_OBJ_FLAG_GESTURE_BUBBLE|LV_OBJ_FLAG_PRESS_LOCK|LV_OBJ_FLAG_SCROLLABLE|LV_OBJ_FLAG_SCROLL_CHAIN_HOR|LV_OBJ_FLAG_SCROLL_CHAIN_VER|LV_OBJ_FLAG_SCROLL_ELASTIC|LV_OBJ_FLAG_SCROLL_MOMENTUM|LV_OBJ_FLAG_SCROLL_WITH_ARROW|LV_OBJ_FLAG_SNAPPABLE);
                            add_style_style_panel_default(obj);
                            lv_obj_set_style_align(obj, LV_ALIGN_CENTER, LV_PART_MAIN | LV_STATE_DEFAULT);
                            lv_obj_set_style_radius(obj, 300, LV_PART_MAIN | LV_STATE_DEFAULT);
                            lv_obj_set_style_bg_color(obj, lv_color_hex(theme_colors[active_theme_index][1]), LV_PART_MAIN | LV_STATE_DEFAULT);
                        }
                        {
                            // LabelRelativeHumidityMeasurementLabel
                            lv_obj_t *obj = lv_label_create(parent_obj);
                            objects.label_relative_humidity_measurement_label = obj;
                            lv_obj_set_pos(obj, 40, 0);
                            lv_obj_set_size(obj, LV_SIZE_CONTENT, LV_SIZE_CONTENT);
                            add_style_label_nav_text_alternate(obj);
                            lv_obj_set_style_align(obj, LV_ALIGN_CENTER, LV_PART_MAIN | LV_STATE_DEFAULT);
                            lv_obj_set_style_text_font(obj, &lv_font_montserrat_32, LV_PART_MAIN | LV_STATE_DEFAULT);
                            lv_label_set_text(obj, "%");
                        }
                        {
                            // LabelHumidtyLevel
                            lv_obj_t *obj = lv_label_create(parent_obj);
                            objects.label_humidty_level = obj;
                            lv_obj_set_pos(obj, -20, 0);
                            lv_obj_set_size(obj, LV_SIZE_CONTENT, LV_SIZE_CONTENT);
                            lv_obj_clear_flag(obj, LV_OBJ_FLAG_CLICK_FOCUSABLE|LV_OBJ_FLAG_GESTURE_BUBBLE|LV_OBJ_FLAG_PRESS_LOCK|LV_OBJ_FLAG_SCROLLABLE|LV_OBJ_FLAG_SCROLL_CHAIN_HOR|LV_OBJ_FLAG_SCROLL_CHAIN_VER|LV_OBJ_FLAG_SCROLL_ELASTIC|LV_OBJ_FLAG_SCROLL_MOMENTUM|LV_OBJ_FLAG_SCROLL_WITH_ARROW|LV_OBJ_FLAG_SNAPPABLE);
                            add_style_style_top_nav_text_normal(obj);
                            lv_obj_set_style_align(obj, LV_ALIGN_CENTER, LV_PART_MAIN | LV_STATE_DEFAULT);
                            lv_obj_set_style_pad_top(obj, 0, LV_PART_MAIN | LV_STATE_DEFAULT);
                            lv_label_set_text(obj, "0");
                        }
                    }
                }
            }
        }
    }
    
    tick_screen_air();
}

void tick_screen_air() {
    tick_user_widget_bottom_nav_bar(120);
}
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
