trailcurrentoss/TrailCurrentWaveshareEsp32s3Remote/src/ui/screens.h

#ifndef EEZ_LVGL_UI_SCREENS_H
#define EEZ_LVGL_UI_SCREENS_H

#include <lvgl.h>

#ifdef __cplusplus
extern "C" {
#endif

typedef struct _objects_t {
    lv_obj_t *home;
    lv_obj_t *trailer;
    lv_obj_t *power;
    lv_obj_t *solar;
    lv_obj_t *air;
    lv_obj_t *settings;
    lv_obj_t *temp;
    lv_obj_t *wifi_setup;
    lv_obj_t *server_config;
    lv_obj_t *home_page_bottom_nav_bar;
    lv_obj_t *home_page_bottom_nav_bar__bottom_nav_bar_button_home;
    lv_obj_t *home_page_bottom_nav_bar__bottom_nav_bar_button_trailer;
    lv_obj_t *home_page_bottom_nav_bar__botttom_nav_bar_button_power;
    lv_obj_t *home_page_bottom_nav_bar__botttom_nav_bar_button_solar;
    lv_obj_t *home_page_bottom_nav_bar__botttom_nav_bar_button_fridge;
    lv_obj_t *home_page_bottom_nav_bar__botttom_nav_bar_button_settings;
    lv_obj_t *label_warning_icon_trailer_connected;
    lv_obj_t *label_warning_text_trailer_connected;
    lv_obj_t *label_warning_icon_fridge;
    lv_obj_t *label_warning_text_fridge;
    lv_obj_t *label_warning_icon_rear_door;
    lv_obj_t *label_warning_text_rear_door;
    lv_obj_t *label_warning_icon_cabinets;
    lv_obj_t *label_warning_text_cabinets;
    lv_obj_t *label_warning_icon_side_door;
    lv_obj_t *label_warning_text_side_door;
    lv_obj_t *label_warning_icon_lights;
    lv_obj_t *label_warning_text_lights;
    lv_obj_t *label_warning_icon_water;
    lv_obj_t *label_warning_text_water;
    lv_obj_t *label_warning_icon_fan;
    lv_obj_t *label_warning_text_fan;
    lv_obj_t *label_warning_icon_stabilizers;
    lv_obj_t *label_warning_text_stabilizers;
    lv_obj_t *label_warning_icon_power;
    lv_obj_t *label_warning_text_power;
    lv_obj_t *trailer_page_bottom_nav_bar;
    lv_obj_t *trailer_page_bottom_nav_bar__bottom_nav_bar_button_home;
    lv_obj_t *trailer_page_bottom_nav_bar__bottom_nav_bar_button_trailer;
    lv_obj_t *trailer_page_bottom_nav_bar__botttom_nav_bar_button_power;
    lv_obj_t *trailer_page_bottom_nav_bar__botttom_nav_bar_button_solar;
    lv_obj_t *trailer_page_bottom_nav_bar__botttom_nav_bar_button_fridge;
    lv_obj_t *trailer_page_bottom_nav_bar__botttom_nav_bar_button_settings;
    lv_obj_t *label_current_speed_value;
    lv_obj_t *label_number_of_satellite_value;
    lv_obj_t *gnss_mode_value;
    lv_obj_t *label_altitude_in_feet_value;
    lv_obj_t *label_current_lat_value;
    lv_obj_t *label_current_long_value;
    lv_obj_t *obj0;
    lv_obj_t *obj1;
    lv_obj_t *power_page_bottom_nav_bar;
    lv_obj_t *power_page_bottom_nav_bar__bottom_nav_bar_button_home;
    lv_obj_t *power_page_bottom_nav_bar__bottom_nav_bar_button_trailer;
    lv_obj_t *power_page_bottom_nav_bar__botttom_nav_bar_button_power;
    lv_obj_t *power_page_bottom_nav_bar__botttom_nav_bar_button_solar;
    lv_obj_t *power_page_bottom_nav_bar__botttom_nav_bar_button_fridge;
    lv_obj_t *power_page_bottom_nav_bar__botttom_nav_bar_button_settings;
    lv_obj_t *panel_control_buttons;
    lv_obj_t *btn_device01;
    lv_obj_t *lbl_device01_status_ind;
    lv_obj_t *lbl_device01_label;
    lv_obj_t *btn_device02;
    lv_obj_t *lbl_device02_status_ind;
    lv_obj_t *lbl_device02_label;
    lv_obj_t *btn_device03;
    lv_obj_t *lbl_device03_status_ind;
    lv_obj_t *lbl_device03_label;
    lv_obj_t *btn_device04;
    lv_obj_t *lbl_device04_status_ind;
    lv_obj_t *lbl_device04_label;
    lv_obj_t *btn_device05;
    lv_obj_t *lbl_device05_status_ind;
    lv_obj_t *lbl_device05_label;
    lv_obj_t *btn_device06;
    lv_obj_t *lbl_device06_status_ind;
    lv_obj_t *lbl_device06_label;
    lv_obj_t *btn_device07;
    lv_obj_t *lbl_device07_status_ind;
    lv_obj_t *lbl_device07_label;
    lv_obj_t *btn_device08;
    lv_obj_t *lbl_device08_status_ind;
    lv_obj_t *lbl_device08_label;
    lv_obj_t *lbl_button_all_label;
    lv_obj_t *panel_brightness_adjustment;
    lv_obj_t *button_brightness_dialog_close;
    lv_obj_t *obj2;
    lv_obj_t *slider_device_brightness_change;
    lv_obj_t *solar_page_bottom_nav_bar;
    lv_obj_t *solar_page_bottom_nav_bar__bottom_nav_bar_button_home;
    lv_obj_t *solar_page_bottom_nav_bar__bottom_nav_bar_button_trailer;
    lv_obj_t *solar_page_bottom_nav_bar__botttom_nav_bar_button_power;
    lv_obj_t *solar_page_bottom_nav_bar__botttom_nav_bar_button_solar;
    lv_obj_t *solar_page_bottom_nav_bar__botttom_nav_bar_button_fridge;
    lv_obj_t *solar_page_bottom_nav_bar__botttom_nav_bar_button_settings;
    lv_obj_t *panel_solar_input;
    lv_obj_t *label_remaining_cacpity_2;
    lv_obj_t *panel_charge_type;
    lv_obj_t *label_solar_status;
    lv_obj_t *panel_shore_power;
    lv_obj_t *label_power_shore_power_heading;
    lv_obj_t *label_shore_power_connection_status;
    lv_obj_t *panel_shore_power_indicator_background;
    lv_obj_t *panel_shore_power_indicator_foreground;
    lv_obj_t *panel_power_battery_stats;
    lv_obj_t *label_power_remaining_cacpity_1;
    lv_obj_t *bar_battery_soc;
    lv_obj_t *label_power_battery_percentage;
    lv_obj_t *label_battery_voltage;
    lv_obj_t *panel_power_remaining_time;
    lv_obj_t *label_power_remaining_cacpity;
    lv_obj_t *power_remaining_arc_group;
    lv_obj_t *power_arc_remaining_hours;
    lv_obj_t *panel_power_remaining_center;
    lv_obj_t *label_time_to_go_measurement_type;
    lv_obj_t *label_power_remaining_time_to_go_value;
    lv_obj_t *label_power_remaining;
    lv_obj_t *label_remaining_cacpity_1;
    lv_obj_t *obj3;
    lv_obj_t *air_page_bottom_nav_bar;
    lv_obj_t *air_page_bottom_nav_bar__bottom_nav_bar_button_home;
    lv_obj_t *air_page_bottom_nav_bar__bottom_nav_bar_button_trailer;
    lv_obj_t *air_page_bottom_nav_bar__botttom_nav_bar_button_power;
    lv_obj_t *air_page_bottom_nav_bar__botttom_nav_bar_button_solar;
    lv_obj_t *air_page_bottom_nav_bar__botttom_nav_bar_button_fridge;
    lv_obj_t *air_page_bottom_nav_bar__botttom_nav_bar_button_settings;
    lv_obj_t *obj4;
    lv_obj_t *label_relative_humidity_header_1;
    lv_obj_t *bar_interior_temperature;
    lv_obj_t *label_interior_temp_value;
    lv_obj_t *label_air_quality_temp_reading_type_label;
    lv_obj_t *panel_relative_humity;
    lv_obj_t *label_relative_humidity_header;
    lv_obj_t *relative_humidity_arc_group;
    lv_obj_t *arc_relative_humidity;
    lv_obj_t *panel_relative_humidity_center;
    lv_obj_t *label_relative_humidity_measurement_label;
    lv_obj_t *label_humidty_level;
    lv_obj_t *setting_page_bottom_nav_bar;
    lv_obj_t *setting_page_bottom_nav_bar__bottom_nav_bar_button_home;
    lv_obj_t *setting_page_bottom_nav_bar__bottom_nav_bar_button_trailer;
    lv_obj_t *setting_page_bottom_nav_bar__botttom_nav_bar_button_power;
    lv_obj_t *setting_page_bottom_nav_bar__botttom_nav_bar_button_solar;
    lv_obj_t *setting_page_bottom_nav_bar__botttom_nav_bar_button_fridge;
    lv_obj_t *setting_page_bottom_nav_bar__botttom_nav_bar_button_settings;
    lv_obj_t *container_display_settings;
    lv_obj_t *btn_theme_light;
    lv_obj_t *lbl_device08_status_ind_5;
    lv_obj_t *btn_theme_dark;
    lv_obj_t *lbl_device08_status_ind_6;
    lv_obj_t *label_screen_timeout;
    lv_obj_t *button_screen_timeout_decrease;
    lv_obj_t *label_screen_timeout_value;
    lv_obj_t *button_screen_timeout_increase;
    lv_obj_t *check_box_keep_screen_on_while_in_motion;
    lv_obj_t *container_connectivity_options;
    lv_obj_t *label_wifi_status_value;
    lv_obj_t *btn_change_wifi;
    lv_obj_t *label_server_url_value;
    lv_obj_t *label_api_key_status;
    lv_obj_t *label_websocket_status;
    lv_obj_t *container_demo_settings;
    lv_obj_t *button_settings_demo_light_sequence_start;
    lv_obj_t *button_settings_demo_light_sequence_stop;
    lv_obj_t *container_about_settings;
    lv_obj_t *label_about_header;
    lv_obj_t *label_version_number;
    lv_obj_t *mcu_mac_address_value;
    lv_obj_t *container_date_time_settings;
    lv_obj_t *label_time_zone_header;
    lv_obj_t *drop_down_selected_time_zone;
    lv_obj_t *label_wifi_setup_title;
    lv_obj_t *btn_wifi_scan;
    lv_obj_t *roller_wifi_networks;
    lv_obj_t *label_wifi_ssid;
    lv_obj_t *textarea_wifi_ssid;
    lv_obj_t *label_wifi_password;
    lv_obj_t *textarea_wifi_password;
    lv_obj_t *btn_wifi_connect;
    lv_obj_t *label_wifi_status;
    lv_obj_t *btn_wifi_skip;
    lv_obj_t *label_server_config_title;
    lv_obj_t *label_server_url;
    lv_obj_t *textarea_server_url;
    lv_obj_t *label_api_key;
    lv_obj_t *textarea_api_key;
    lv_obj_t *btn_save_server_config;
    lv_obj_t *btn_server_config_back;
    lv_obj_t *label_server_config_status;
} objects_t;

extern objects_t objects;

enum ScreensEnum {
    SCREEN_ID_HOME = 1,
    SCREEN_ID_TRAILER = 2,
    SCREEN_ID_POWER = 3,
    SCREEN_ID_SOLAR = 4,
    SCREEN_ID_AIR = 5,
    SCREEN_ID_SETTINGS = 6,
    SCREEN_ID_TEMP = 7,
    SCREEN_ID_WIFI_SETUP = 8,
    SCREEN_ID_SERVER_CONFIG = 9,
};

void create_screen_home();
void tick_screen_home();

void create_screen_trailer();
void tick_screen_trailer();

void create_screen_power();
void tick_screen_power();

void create_screen_solar();
void tick_screen_solar();

void create_screen_air();
void tick_screen_air();

void create_screen_settings();
void tick_screen_settings();

void create_screen_temp();
void tick_screen_temp();

void create_screen_wifi_setup();
void tick_screen_wifi_setup();

void create_screen_server_config();
void tick_screen_server_config();

void create_user_widget_bottom_nav_bar(lv_obj_t *parent_obj, int startWidgetIndex);
void tick_user_widget_bottom_nav_bar(int startWidgetIndex);

enum Themes {
    THEME_ID_DEFAULT,
    THEME_ID_DARK,
};
enum Colors {
    COLOR_ID_ACCENT_COLOR,
    COLOR_ID_BACKGROUND_BLACK,
    COLOR_ID_BACKGROUND_CONTENT,
    COLOR_ID_BACKGROUND_NOT_SELECTED,
    COLOR_ID_BACKGROUND_PANEL,
    COLOR_ID_BACKGROUND_SELECTED,
    COLOR_ID_COOL,
    COLOR_ID_FOREGROUND_WHITE,
    COLOR_ID_HOT,
    COLOR_ID_PRIMARY_TEXT_COLOR,
    COLOR_ID_SECONDARY_TEXT_COLOR,
    COLOR_ID_SUCCESS,
};
void change_color_theme(uint32_t themeIndex);
extern uint32_t theme_colors[2][12];
extern uint32_t active_theme_index;

void tick_screen_by_id(enum ScreensEnum screenId);
void tick_screen(int screen_index);

void create_screens();


#ifdef __cplusplus
}
#endif

#endif /*EEZ_LVGL_UI_SCREENS_H*/
