trailcurrentoss/TrailCurrentWaveshareEsp32s3Remote/src/ui/ui_font_fa32.c

/*******************************************************************************
 * Size: 32 px
 * Bpp: 1
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
    0x0, 0x0, 0x0, 0x0, 0x0, 0x0, 0x0, 0x0,
    0x3f, 0xff, 0xff, 0xfc, 0x3f, 0xff, 0xff, 0xfc,
    0x3f, 0xff, 0xff, 0xfc, 0x3f, 0xff, 0xff, 0xf8,
    0x1f, 0xff, 0xff, 0xf8, 0xf, 0xff, 0xff, 0xf0,
    0xf, 0xff, 0xff, 0xf0, 0xf, 0x0, 0x0, 0xf0,
    0xf, 0x0, 0x0, 0xf0, 0x6, 0x0, 0x0, 0x60,
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
