trailcurrentoss/TrailCurrentWaveshareEsp32s3Remote/src/ui/actions.h

#ifndef EEZ_LVGL_UI_EVENTS_H
#define EEZ_LVGL_UI_EVENTS_H

#include <lvgl.h>

#ifdef __cplusplus
extern "C" {
#endif

extern void action_change_screen(lv_event_t * e);
extern void action_settings_selection_change(lv_event_t * e);
extern void action_change_theme(lv_event_t * e);
extern void action_timeout_changed(lv_event_t * e);
extern void action_keep_on_while_driving_changed(lv_event_t * e);
extern void action_timezone_change(lv_event_t * e);
extern void action_wifi_scan(lv_event_t * e);
extern void action_wifi_connect(lv_event_t * e);
extern void action_save_server_url(lv_event_t * e);
extern void action_save_api_key(lv_event_t * e);
extern void action_save_server_config(lv_event_t * e);
extern void action_toggle_light(lv_event_t * e);
extern void action_navigate_to_wifi_setup(lv_event_t * e);


#ifdef __cplusplus
}
#endif

#endif /*EEZ_LVGL_UI_EVENTS_H*/
