trailcurrentoss/TrailCurrentWaveshareEsp32s3Remote/src/ui/images.h

#ifndef EEZ_LVGL_UI_IMAGES_H
#define EEZ_LVGL_UI_IMAGES_H

#include <lvgl.h>

#ifdef __cplusplus
extern "C" {
#endif

extern const lv_img_dsc_t img_trailer_back;
extern const lv_img_dsc_t img_trailer_side;

#ifndef EXT_IMG_DESC_T
#define EXT_IMG_DESC_T
typedef struct _ext_img_desc_t {
    const char *name;
    const lv_img_dsc_t *img_dsc;
} ext_img_desc_t;
#endif

extern const ext_img_desc_t images[2];


#ifdef __cplusplus
}
#endif

#endif /*EEZ_LVGL_UI_IMAGES_H*/
